2solve/EMB2-2609-V5/Desenvolvimento_IC2S-EBM2-2609-V5.0/Documentos_IC2S-EBM2-2609-V5.0/01-Esquemáticos_IC2S-EBM2-2609-V5.0/png/IC2S_Extension_Board-EBM2_V5-4 Barreira digital.png

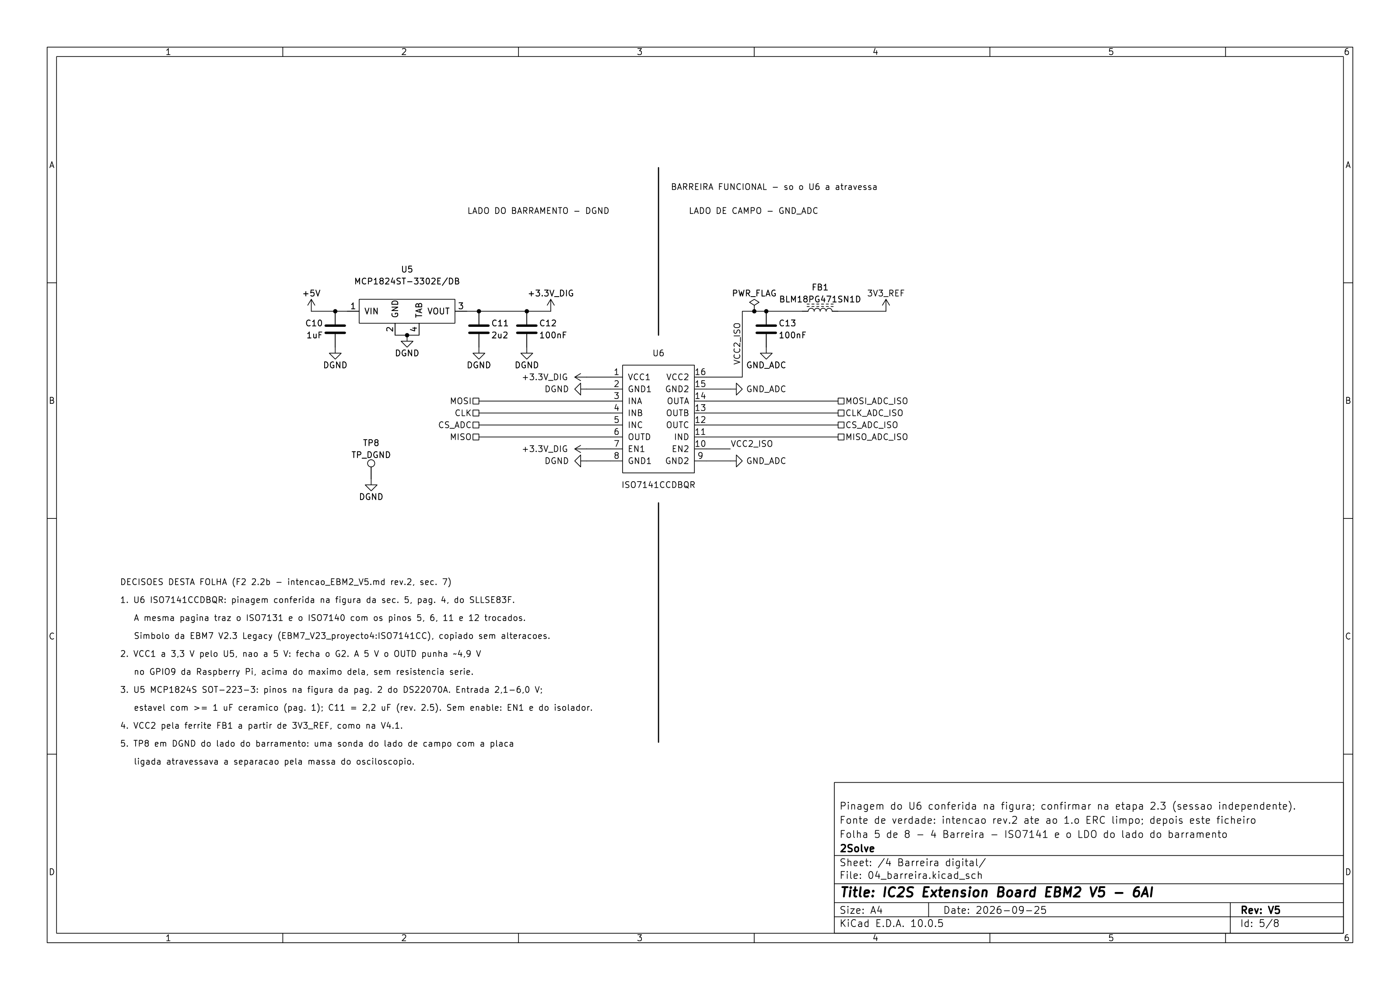
Desenvolvimento_IC2S-EBM2-2609-V5.0/Documentos_IC2S-EBM2-2609-V5.0/01-Esquemáticos_IC2S-EBM2-2609-V5.0/png/IC2S_Extension_Board-EBM2_V5-4 Barreira digital.png
