2solve/EMB2-2609-V5/Desenvolvimento_IC2S-EBM2-2609-V5.0/Documentos_IC2S-EBM2-2609-V5.0/00-Especificações_Técnicas_IC2S-EBM2-2609-V5.0/Verificacoes_F2/verificacao_2_3b_rev25/intencao_EBM2_V5.md

# Documento de intenção — IC2S Extension Board EBM2 V5 (6AI)

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

---

## 1 · O que este documento decide, em poucas linhas

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

## 2 · Estrutura de folhas e designadores

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

### Correspondência V4.1 → V5 das peças herdadas

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

## 3 · Trilhos e domínios

| Rede | Domínio | Origem | Quem a usa |
|---|---|---|---|
| `+24V` | campo, sem isolamento | `P1.20` | folha 02 |
| `GND_24V` | campo | `P1.19` | folha 02, unida a `GND_ADC` por `R200` |
| `+24V_ADC` | campo | `F202` → `D202` | folha 06, laços |
| `+24V_REG` | campo | `F201` → `D201` → `R206` | folha 03 |
| `+5V_ADC` | campo | `TPS7A4001` | folha 03 |
| `+12V_TPS` | campo | `U640` `TPS7A4001` a partir de `+24V_ADC` (**rev. 2.4**) | folha 06, `+Vs` dos `U601`-`U606` |
| `3V3_REF` | campo | `SPX3819`, grampo `TL431` | folhas 03, 04 (`VCC2`), 05, 06 (clamps) |
| `+2V5_REF` | campo | `ADR4525` | folhas 05 (`VREF`) e 07 (topo do divisor) |
| `GND_ADC` | campo | — | todas as de campo |
| `+5V` | **barramento** | `P1.17` | folha 04, entrada do `MCP1824S` |
| `+3.3V_DIG` | **barramento** | `MCP1824S` | folha 04, `VCC1` e `EN1` do isolador |
| `DGND` | **barramento** | `P1.3`, `P1.12`, `P1.16` | folha 04 |

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

## 4 · Folha 01 — conectores

### Ligações, como especificação

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

### Porquê

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

### DFT

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

## 5 · Folha 02 — entrada de 24 V *(desenhada)*

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

**Acrescenta-se nesta folha**, por DFT e por LED (§11):

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

## 6 · Folha 03 — alimentação *(desenhada)*

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

## 7 · Folha 04 — barreira

### Ligações, como especificação

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

`T400`, ponto de prova em `DGND`, **deste lado da barreira**.

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

### Porquê

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

### Dimensionamento

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

### Lógica activa

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

## 8 · Folha 05 — conversor

### Ligações, como especificação

**`U500`, `MCP3208T-BI/SL`**, SOIC-16. Pinagem lida na figura da pág. 1 do
`DS21298E`:

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

### Porquê

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

### Restrições que o firmware tem de cumprir

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

## 9 · Folha 06 — seis laços

### Ligações, como especificação

Por canal *k*, de 1 a 6. Exemplo do canal 1:

`+24V_ADC` → fusível `F601` → `LOOP1_V+`, que vai ao pino 2 de `P2` e alimenta o
transmissor. O retorno chega por `AIN1-`, pino 3 de `P2`. Desse nó sai o TVS
`D601` (cátodo no nó, ânodo a `GND_ADC`) e o **protector de laço `U601` `TPS26613DDFR`**
(**rev. 2.4**, como a EBM7 V2.3 Legacy `U8`-`U11`): pino 4 `IN` no nó `AIN1-`, pino 5 `OUT` em
`AIN1_LIM`, pino 6 `+Vs` em `+12V_TPS` com `C611` 100 nF, pino 7 `VSNS` na rede `VSNS`, pinos
1 `GND`, 2 `MODE` e 3 `−Vs` a `GND_ADC`, pino 8 `SGOOD` sem ligação. ~~`AL5809` e `BAT46W`
antiparalelo~~ saem. De `AIN1_LIM` sai `R601`, **0 Ω 0603** (a posição do `R10` da Legacy). O
outro terminal de `R601` é o nó de medida: burden `R611` 110 Ω a `GND_ADC` e antialias `R621`
3,3 kΩ. O outro terminal de `R621` forma `AIN1_ADC`, com `C601` 100 nF a
`GND_ADC` e o clamp `D621` `BAV199`: pino 3 no sinal, pino 1 a `GND_ADC`, pino 2
a `3V3_REF` (figura da pág. 1 do `BAV199LT1/D`). O TVS `D611` fica entre
~~`+24V_ADC`~~ **`LOOP1_V+`, depois do fusível `F601`, no lado do terminal** (rev. 2.3), e `GND_ADC`.

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

| Peça | Valor | Part number | Pegada | Origem |
|---|---|---|---|---|
| Fusível | 50 mA | `3413.0002.22` | 1206 | Legacy |
| TVS trilho `D611`-`D616` | ~~30 V~~ **36 V** | ~~`824500301`~~ **`824520361`** (SMBJ36A, 600 W) | **DO-214AA** | **rev. 2.2**: a 32 V o trilho chega a 31,4 V, acima dos 30 V de standoff do anterior. É o da EBM7 |
| TVS retorno `D601`-`D606` | ~~36 V~~ **33 V** | **`SMBJ33A-13-F`** (Diodes, a família do `SMBJ36A-13-F` da Legacy) — **datasheet a conferir no pacote da BOM** | DO-214AA | **rev. 2.4**: ver «Porquê» |
| Protector de laço | 25-40 mA, R_ON 4,8-12,5 Ω | ~~`AL5809-25P1-7`~~ **`TPS26613DDFR`** | **SOT-23-8** (md5 igual à Legacy) | **rev. 2.4**, Legacy `U8`-`U11` |
| Desacoplamento `+Vs` | 100 nF 100 V | `GRM188R72A104KA35D` (`C611`-`C616`) | 0603 | Legacy `C26`/`C29`/`C31`/`C32` |
| ~~Schottky antiparalelo~~ | — | ~~`BAT46W-7-F`~~ | — | **sai na rev. 2.4**: o TPS26613 aguenta ±55 V |
| Série | ~~249 Ω~~ ~~150 Ω~~ ~~100 Ω~~ **0 Ω** | `RC0603JR-070RL` | **0603** | **rev. 2.4**: Legacy `R10`; o curto é do `U60x` |
| Burden | 110 Ω 0,1 % 25 ppm | ~~`ERA3AEB111V`~~ **`ERA8AEB111V`** | **1206** | F1 §2.5; **rev. 2.1** |
| Antialias | 3,3 kΩ | `RC0603FR-073K3L` | 0603 | V4.1 |
| Filtro | 100 nF | como V4.1 | 0603 | V4.1 |
| Clamp | — | `BAV199LT1G` | SOT23-3 | Legacy |

`D630` + `R630` 14,7 kΩ: LED de `+24V_ADC` a `GND_ADC`, substitui `D19` (§11).

### Porquê

- **Rev. 2.4 (2026-09-24, decidida pelo projectista): o limitador passa a ser o da EBM7 V2.3
  Legacy, `TPS26613DDFR`** («copiemos como está el EBM7»). A 2.3b reprovou o `AL5809` em três
  linhas (F1 térmica em curto, F2 sempre abaixo dos 2,5 V mínimos, F9 −0,40 V contra −0,3 V).
  Citações do `SLVSFE3C` (TI, rev. C, dez. 2021), na pasta de referências da EBM7:
  - *Curto do transmissor (F1).* `MODE` a `GND`: limita a `I(OL)` 25-40 mA (pág. 5) durante
    `tOL_Expiry` 100 ms, corta, e tenta de novo a cada `tRETRY1` 800 ms (tabela 8-3, pág. 23;
    o `26613` é o de «auto-retry», tabela da pág. 3). No pior caso, a 32 V, com `IN` a
    31,0 V e `OUT` a 40 mA × 110 Ω = 4,4 V, **1,06 W durante 100 ms em cada 900 ms: 0,12 W
    de média, +14 °C** (RθJA 117,8 °C/W, pág. 4). A fig. 7-19 (pág. 12, típica, placa da TI)
    dá, a 85 °C e ~1,05 W, **~200 ms até ao corte térmico** (160 °C): o temporizador de
    100 ms corta antes. Não depende de cobre na F3. **Confirmar no T26.**
  - *Tensão mínima (F2).* Não há: dentro do limite é um interruptor de 4,8-12,5 Ω
    (`RON`, pág. 6). A 20 mA cai **≤ 0,25 V**, contra os 1,6-2,5 V do `AL5809`.
  - *Inversão (F9).* `IN` e `OUT` aguentam ±55 V (pág. 4). Com `−Vs` a `GND`, `OUT` abaixo de
    `−Vs` − 0,2 V corta o FET (`VO_UVLO`, pág. 6, só no 26613/14). **O `BAT46W` sai.**
  - *Alimentação.* Precisa de `+Vs` entre 3 e 30 V (pág. 4) e **acima da tensão de `OUT`**, ou
    corta por `VOUT_OVLO` (`+Vs` + 0,05 V, pág. 5). `OUT` chega a 4,4 V no limite. Copia-se a
    Legacy: **`U640` `TPS7A4001` a 12,09 V** (`R641` 93k1 / `R642` 10k: 1,173 × 10,31) a partir de
    `+24V_ADC`. O `+24V_ADC` não serve: a 32 V fica a 31,4 V, acima dos 30 V recomendados.
    Consumo: 6 × 1,65 mA máx. (pág. 6) + divisores ≈ **10,8 mA**; a 32 V são 0,21 W no `U640`,
    +14 °C (RθJA 66,7 °C/W, SBVS162B pág. 4).
  - *Condensadores do `U640`* (SBVS162B pág. 1 e §8.2.2.2: saída **> 4,7 µF sobre temperatura
    e tolerância**, entrada ≥ 1 µF, recomendados 10 µF). Copiam-se os da Legacy: `C642`
    10 µF 50 V 1206 X5R (`C3216X5R1H106K160AB`, Legacy `C38`; a 12 V a curva da TDK tem de
    dar > 4,7 µF — conferir na BOM) e `C640` 10 µF 100 V 1210 + `C641` 100 nF na entrada
    (Legacy `C35`/`C36`). *A EBM7 V2.3 não Legacy tinha 4,7 µF 25 V 0805: não cumpria.*
  - *`VSNS`* (tabela 8-2, pág. 20). A Legacy tem `R22` 11k5 / `R23`‖`R24` 6k65 → limiar
    descendente 4,46 V. A nota (2) pede-o **acima** de `I_LOOP` × `R_burden`: com `I(OL)` máx.
    40 mA × 110 Ω = 4,40 V, a margem é de 1,4 %, e o `V(SNSF)` de 1 V vem sem mínimo nem
    máximo. **Desvio da Legacy: `R643` 13k3** → limiar descendente **5,0 V** (margem 14 %),
    ascendente 1,72 × 5,0 = **8,6 V** contra `+Vs` mín. 11,8 V; `VSNS` = 2,4 V ≤ 5 V; `R1+R2`
    = 16,6 kΩ ≤ `+Vs`/45 µA = 262 kΩ. `R644`/`R645` 6k65 e `C643` 100 nF, como a Legacy.
  - *`SGOOD` sem ligação*, como na Legacy. **Decisão escrita** (a 2.3b da Legacy pedia-a):
    não há GPIO livre do lado de campo; a falha vê-se na leitura.
  - *`R601` a 0 Ω.* A série de 100 Ω só existia para aguentar o curto sem limitador (V4.1);
    com o limite de 40 mA não protege nada. Fica a ilha, como na Legacy (`R10`). Ganho: +2,0 V
    ao transmissor.
  - *TVS do retorno a 33 V.* `IN` do TPS26613 aguenta **55 V**; o SMBJ36A grampeia a
    **58,1 V** (Würth 824520361, pág. 1). A Legacy usa 30 V (grampo 48,4 V), mas com 30 V de
    standoff os 31,4 V do retorno em curto a 32 V ficam acima (a razão da rev. 2.2). **33 V**:
    standoff 33 V > 31,4 V, grampo 53,3 V a 11,3 A (a classe 33 V do `D200`, Bourns
    SMA6J33A pág. 2) < 55 V. Os `D611`-`D616`, no `LOOPk_V+`, não estão no `IN` e ficam a 36 V.
  - *Comportamento que muda para o firmware.* Em curto a leitura **alterna**: 100 ms a 4095
    (25-40 mA) e 800 ms a ~0 mA (FET desligado → `"null"`). Com a média de 10 amostras em 500
    ms o painel verá sobretudo `"null"`. Avisar o Rodrigo: um `"null"` intermitente com picos a
    4095 é curto, não laço aberto.
  - *Sem `+12V_TPS`* (por exemplo `U640` avariado), o TPS26613 passa ao modo de laço (pág. 20):
    conduz com 5-8,5 V de queda e limita a 22-45,5 mA. A medida continua se o transmissor
    tiver tensão.
- **Topologia copiada da V4.1**, com três valores mudados e já justificados na
  F1: burden 110 Ω, clamp `BAV199`, fusível de 50 mA.
- **Rev. 2.3 (2026-09-23): os seis TVS de laço passam para depois do fusível de canal, no
  terminal `LOOPk_V+`** — como na EBM7 Legacy (`D9`/`D10`/`D12`/`D13` em `+24V_AINk`). Um TVS em
  curto abre só o fusível do seu canal, em vez do `F202` e dos seis canais; um surto do campo
  descarrega no terminal sem atravessar o fusível (resta ~2,9 A de pico entre o grampo de
  58 V e o trilho de 31 V: aguenta 8/20 µs, pode abrir em 10/1000 µs); os surtos da fonte
  ficam só com o `D200` (simplifica a `V7`). Custo: uma fonte externa > 36 V ligada a um
  `LOOPk_V+` leva o TVS desse canal, e só desse. Sem efeito na medida.
- ~~**Os seis TVS de trilho ficam, agora num trilho só.**~~ *(texto da rev. 2, ultrapassado)* Na V4.1 havia dois
  trilhos isolados com três TVS cada. Com um trilho, seis é redundante, mas
  mantém um TVS junto de cada par de pinos de `P2`, que é onde a sobretensão
  entra. A interacção com o `D200` analisa-se na 2.3b (`V7`).
- **O fusível de canal passa a 1206**, porque a peça da Legacy é 1206. O da V4.1
  era 0603. O layout desta zona muda de qualquer forma.
- *[Ultrapassado pela rev. 2.4: fica como histórico da escolha do AL5809.]*
  **Rev. 2.1 (2026-09-23, decidida pelo projectista): limitador por canal, fecha a
  `V8`.** Um transmissor em curto fazia passar 74 mA a 28 V e punha 1,4 W na série
  0603 — defeito herdado da V4.1, cujos `PDM2` não limitavam (curto 1 s, sem
  protecção de sobrecarga). O `AL5809-25` garante 23,75-26,25 mA de −40 a +125 °C
  (DS36625 rev. 5, pág. 4): acima dos 22,7 mA de saturação, logo não se perde
  leitura, e o alarme de 21 mA da NE43 lê-se. **No retorno**, em série com o burden,
  não altera a medida; um curto do `+` à massa não passa por ele e continua a abrir
  o fusível de 50 mA (é essa a razão do fusível, que faltava escrever). O `BAT46W`
  (100 V; V_F máx. 0,25 V a 0,1 mA e 0,45 V a 10 mA, Vishay 86406) protege o −0,3 V
  do `AL5809`; a ~3 mA de falha inversa ficam ~0,40 V, **acima dos −0,3 V: resíduo
  a confirmar na 2.3b**. Série a 150 Ω e burden em 1206 para aguentarem os 26 mA.
  Contas em `ferramentas/avalia_opcoes_V8_RE1.py` e no
  `Relatorio_Melhorias_Isolamento_V8_RE1_2026-09-23.md`. **Pegada do AL5809: Type B,
  duas ilhas iguais — não o PowerDI-123 do KiCad.**

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

### Prova de uma multiplicação

**Rev. 2.4 (TPS26613, `R601` 0 Ω).** A 18 V, 20 mA, `I_tot` = 6 × 20 mA + 10,8 mA (`U640`)
+ 1,5 mA (LED) = 132 mA:

| Parcela | Conta | Queda |
|---|---|---|
| `F202` | 0,8 Ω × 0,132 A | 0,11 V |
| `D202` | V_F máx. a 0,13 A (fig. 2 do MBR1H100SF) | 0,50 V |
| `F60x` | 9,2 Ω × 20 mA | 0,18 V |
| `U60x` | `RON` máx. 12,5 Ω × 20 mA | 0,25 V |
| `R601` + burden | (0 + 110 Ω) × 20 mA | 2,20 V |
| **Sobra ao transmissor** | 18 − 3,24 | **≥ 14,76 V** (era ≥ 10,5 V com o AL5809 e 100 Ω) |

Curto a 32 V: `IN` = 31,4 − 9,2 Ω × 40 mA = 31,0 V; `OUT` = 4,4 V; 26,6 V × 40 mA = 1,06 W
durante 100 ms a cada 900 ms. Burden: 40 mA² × 110 Ω = 0,18 W em pico, 0,02 W de média
(`ERA8AEB111V`, 1206, 0,25 W). Pino do ADC: 4,4 V → pelo `R621` 3,3 kΩ e pelo `BAV199` a
`3V3_REF` ≈ 0,15 mA durante 100 ms (a `V10` continua aberta, por construção).

*Texto das revisões anteriores:*

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

## 10 · Folha 07 — termístor

### Ligações, como especificação

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

### Porquê

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

## 11 · LED indicadores — proposta, a confirmar

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

## 12 · DFT

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

Nove, que é o que `RD1` pede. Três fiduciais na folha 01.

## 13 · Orçamento de erro — resumo

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

## 14 · Verificações abertas

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

## 15 · O que NÃO muda

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

## 17 · Rev. 2.5 — correcções da 2.3b rev. 2.4 (2026-09-24; **2.5b**: R204 4k12 depois de conferir o TL431BQ)

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

| # | Peça | Antes → depois | Porquê (conta e fonte) |
|---|---|---|---|
| 1 | `R206` | 33 Ω → **68 Ω** 0805 anti-surto (MPN: `V5`) | `RA2` do `F201` a 32 V, mesmo método da 2.3b, com os dados do Eaton 4309 pág. 2 (CC12H250mA: resistência a frio típ. 3,5 Ω, I²t de pré-arco típ. 3,8·10⁻⁴ A²s medido a 10 × In, nota 3; confirmado no texto e na imagem da tabela). A curva I²t-tempo da pág. 4 dá ≈ 6·10⁻⁴ a 1,5·10⁻³ A²s a 0,1-0,5 ms, a duração real do arranque: **a margem abaixo é conservadora**. Conta: `V²·C200/(2R)` + `I_LIM²·t` da carga a jusante (`C202` a 5 V, o trilho `3V3_REF` e `C207`). Com os condensadores novos: 47 Ω → **9,4×** (falha), 56 Ω → 10,3×, **68 Ω → 11,2×**. A 18 V, ~7 mA de carga: 0,48 V em `R206`, o `U200` recebe ~17 V (mín. 7 V). Pico 0,45 A, ~1,1 mJ por arranque |
| 2 | `U201` | `SPX3819M5-L-3-3` → **`MCP1824T-3302E/OT`** (SOT-23-5) | O TL431 precisa de > 6 µF no cátodo (fig. 6-18, SLVS543S pág. 18, curva A: fronteira direita ≈ 4,5-6 µF) e o `SPX3819` só especifica electrolítico/tântalo («bench testing is the best method»). O `MCP1824` é estável com cerâmico ≥ 1 µF e recomenda ≤ 22 µF (DS22070A §4.3, pág. 19); VIN 2,1-6,0 V; VOUT 3,3 V ± 2,5 % (pág. 8). Pinagem SOT-23-5 fixa 1 VIN · 2 GND · 3 SHDN · 4 PWRGD · 5 VOUT (tabela 3-1, pág. 17), a mesma geometria do `SPX3819`: muda só o pino 4 |
| 3 | `C208` | 10 nF → **sai** | Era o `BP` do `SPX3819`. No `MCP1824` o pino 4 é `PWRGD` (dreno aberto): fica sem ligação. `EN_3V3` passa a `SHDN_3V3` (`R203` 100 kΩ a `VIN`; limiar máx. 45 % de VIN, §4.6 pág. 20) |
| 4 | `C204` | 2,2 µF → **10 µF 50 V X5R 1206 `C3216X5R1H106K160AB`** | Curva da TDK (ProductDetailed, pág. 2): ≈ 9,4 µF a 3,3 V. Pior caso −10 % −15 % (X5R) → 7,2 µF + 1,3 µF do resto do trilho = **8,5 µF > 6 µF**. Nominal 11,4 µF ≤ 22 µF do `MCP1824` |
| 5 | `R204` | 4k42 → ~~4k22~~ **4k12** (`RC0603FR-074K12L`, **rev. 2.5b**) | TL431**BQ**, tabela 6.13 do SLVS543S (pág. 14): V_ref 2,483-2,507 V a 25 °C; **V_I(dev) 34 mV** (máx.−mín. em −40…125 °C; a 1.ª conta usou 17 mV de memória, errado); I_ref 4 µA + I_I(dev) 2,5 µA; \|z_KA\| 0,5 Ω; ΔV_ref/ΔV_KA −2,7 mV/V. Conservador (os 34 mV inteiros para cada lado, R a 1 %, 46 mA da falha dupla): 4k22 → 3,451-3,688 V (**12 mV** sob 3,70 V); **4k12 → 3,427-3,662 V: 38 mV sob 3,70 V (`RA4`) e 45 mV sobre os 3,3825 V do `MCP1824` (+2,5 %, pág. 8)**, o TL431 não conduz em regime. Os 3,70 V são critério de aceite (`RA4`), não máximo absoluto de peça (MCP3208 7 V, ISO7141 6 V, ADR4525 15 V). I_min real 0,7 mA (não 1 mA) |
| 6 | `C207` | 1,0 µF → **2,2 µF** | Estava no mínimo da tabela 11 do ADR45xx (pág. 35) |
| 7 | `C402` | 1,0 µF → **2,2 µF** | Estava no mínimo do `MCP1824` (§4.3) |
| 8 | `C209`, `C645` | **novos**, 10 nF entre `OUT` e `FB` do `U200` e do `U640` | `C_BYP` (SBVS162B nota 4 pág. 5, §8.2.2.3 pág. 11: «TI highly recommends»). Zero em 1/(2π·32,4 kΩ·10 nF) = 491 Hz (`U200`) e 171 Hz (`U640`) |
| 9 | `C644` | **novo**, 10 µF 50 V `C3216X5R1H106K160AB` em paralelo com `C642` | Curva TDK a 12,6 V ≈ 5,8 µF; com −10 % e −15 % (X5R garantido) uma peça dá 4,4 µF **< 4,7 µF** (SBVS162B pág. 1). Duas: **8,9 µF** |
| 10 | `R661`-`R666` | **novas**, 4k7 0603 (`RC0603FR-074K7L`) entre o nó do filtro (`AINk_FILT`: `C60k`, `D62k`) e o pino do ADC (`AINk_ADC`) | Em curto (`I(OL)` 40 mA × 110 Ω = 4,4 V) o `BAV199` conduz ~0,15 mA e cai **≈ 0,67 V a 25 °C, ≈ 0,72 V a 0 °C** (fig. 2 do BAV199LT1/D): o nó fica acima de `VDD` + 0,6 V por construção (a `V10`). A série limita a corrente para o díodo interno do MCP3208 (modelado com 0,6 V, fig. 4-1 do DS21298E) a **(0,74 − 0,6)/4,7 kΩ ≈ 30 µA**. Custo: fuga típica ≤ 2 nA (fig. 2-39) × 4,7 kΩ ≈ 9 µV; no máximo da tabela (±1 µA) 4,7 mV = 7,7 LSB de offset, que a calibração de campo remove. A carga do C_sample de 20 pF por 4,7 kΩ + 1 kΩ: τ = 114 ns contra 75 µs de amostragem. **Não prova** o limite absoluto de tensão, que o datasheet só dá em tensão: prova-se no T26 e pede-se à Microchip a corrente de injecção |

**Não muda, e porquê:**
- `R601` = 0 Ω. Na falha dupla (`U60x` em curto + 30 V injectados) o burden vê 273 mA / 8,2 W. Voltar a
  100 Ω poria `OUT` a 8,4 V no limite de corrente e o `VSNS` deixava de ter solução entre os 4,4 V e o
  `+12V_TPS` mín. 11,58 V. **Aceite como falha dupla**, documentada.
- `V13` (`+5V_IC` com grampo de 9,2 V contra os 6,5 V do `U401`): medir o barramento num painel.
- O «mínimo de 1 mA» do TL431 (recálculo Sonnet): numa falha simples a corrente injectada (≤ 0,15 mA por
  canal) é menor que a carga de `3V3_REF` (~4 mA); o LDO fornece menos e o TL431 nem conduz. Só a falha
  dupla (46 mA) o põe a regular, bem acima de 1 mA.
- A fig. 7-19 do TPS26613 lida pela 2.3b dá ~140 ms até ao corte térmico a 85 °C (a §9 lia ~200 ms):
  continua acima dos 100 ms do temporizador, com menos margem. Confirmar no T26.

## 16 · Porta de verificação da revisão

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
