2solve/EMB2-2609-V5/Desenvolvimento_IC2S-EBM2-2609-V5.0/Documentos_IC2S-EBM2-2609-V5.0/00-Especificações_Técnicas_IC2S-EBM2-2609-V5.0/Verificacoes_F2/verificacao_2_3b_rev25/planejamento_pcb_EBM2_V5.md

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

# Planejamento do PCB — EBM2 V5

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

---

## 1 · Sumário do produto

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

## 2 · Tabela mestre de componentes

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

> **Designadores definitivos** estão em `intencao_EBM2_V5.md` rev. 2, §2: `U4` passa a `U400`, `U5` a `U500`, o `MCP1824` a `U401`, `R5`/`R8` a `R700`/`R701`. Os desta tabela são os da F1.

### 2.1 · Núcleo de medida

| Ref | Função | Part number | Origem | Justificação |
|---|---|---|---|---|
| `U5` | ADC 12 bits SPI, 8 canais | **`MCP3208T-BI/SL`** | **[HERD]** alterado | **MUDA de `-CI` para `-BI`**: mesmo encapsulamento e pinagem, INL de ±1 LSB em vez de ±2. Ver §2.7b |
| `U4` | Isolador digital 4 canais | `ISO7141CCDBQR` | **[HERD]** | Única barreira da placa. Limiares **TTL**, VIH 2,0 V |
| `U202` | Referência de tensão 2,5 V | `ADR4525BRZ` | **[EBM7]** | ±0,02 % inicial; **4 ppm/°C pelo método bowtie**, que é o que conta a partir de 25 °C. Substitui `VREF` = `VDD` |
| `R×6` | Burden dos laços, 110 Ω | `ERA3AEB111V` (Panasonic) | **[NOVO]** valor | ±0,1 % e ±25 ppm/°C. **É o melhor que existe a 110 Ω — ver §2.5** |
| `R×6` | Série de protecção, 249 Ω | `RC0603FR-07249RL` | **[HERD]** | Não se toca: é protecção. Revisão na 2.3b |
| `R×6` | Anti-aliasing, 3,3 kΩ | `RC0603FR-073K3L` | **[HERD]** | Corte a 482 Hz com 100 nF. **O condensador é o reservatório de carga do ADC — ver §2.7d** |
| `R8` | Divisor do NTC, 5,62 kΩ | `ERA3AEB5621V` | **[HERD]** | Já na V4.1. **Passa a pender de `+2V5_REF` e não de `3V3_REF` — ver §2.7e** |
| `R5` | Termístor de placa, 10 kΩ | `NTCS0603E3103JLT` | **[HERD]** | Canal 4 do ADC. Sensor de temperatura da própria placa |
| `C_VDD` | Desacoplamento do ADC, 1 µF | cerâmico X7R 0603 | **[NOVO]** | **O datasheet pede 1 µF, a V4.1 tem 100 nF.** §6.4, pág. 23 |
| `C_VREF` | Desacoplamento da referência, 1 µF | cerâmico X7R 0603 | **[NOVO]** | Figura 6-3, pág. 23 |
| `D×6` | Clamp de entrada | `BAV199` | **[EBM7]** | Substitui `BAT54S`. Fuga 5 nA a 25 °C contra µA do Schottky |
| `D×12` | TVS de campo, 30 V | `824500301` (Würth) | **[HERD]** | Dois por canal |

### 2.2 · Entrada e protecção de 24 V

| Ref | Função | Part number | Origem | Justificação |
|---|---|---|---|---|
| `D200` | TVS de entrada, 33 V | `SMA6J33A-Q` (Bourns) | **[EBM7]** | A V4.1 **não tem TVS nenhum** na entrada. Grampeia a 58,1 V @ 11,3 A |
| `F202` | Fusível rama dos laços | `CC12H750MA-TR` (Eaton) | **[EBM7]** | I²t de fusão **0,15 A²s**. Margem de arranque **41,7×** — ver §2.6 |
| `F201` | Fusível rama do regulador | `CC12H250MA-TR` (Eaton) | **[EBM7]** família | **MUDOU.** Era «100 mA»; **a série não tem 100 mA**, começa em 250 mA |
| `R206` | Limitador de arranque, 22 Ω 0805 | resistência de impulso, 0805 | **[NOVO]** | **Peça nova, obrigatória.** Sem ela `F201` não cumpre `RA2` — ver §2.6 |
| `D201`, `D202` | Bloqueio, 100 V | `MBR1H100SF` | **[EBM7]** | `D201` serve o regulador e `D202` os laços, como no esquemático. Substitui o zener `D26` em série da V4.1; o `PMEG6010CEH` de 60 V é curto contra 58,1 V |
| `R200` | Net-tie das massas, 0 Ω | `RC0603JR-070RL` | **[EBM7]** | Único caminho `GND_24V` ↔ `GND_ADC` |
| `C200` | Entrada do regulador, 2,2 µF/100 V, **1206** | **MPN por fixar — V6** | **[NOVO]** | Pequeno **de propósito**: é ele que fixa a energia de arranque. **Correcção 2026-09-23:** esta linha dava `GRM31CR72A225KA73L` com origem EBM7. **A EBM7 Legacy não tem nenhum 2,2 µF de 100 V**: os seus 2,2 µF são `C1608X5R1E225K080AB`, 0603 de 25 V, e era daí que vinha a pegada 0603 herdada. O part number não consta do catálogo Murata da pasta. Especificação: 2,2 µF, ≥ 100 V, X7R, 1206, ≥ 1 µF efectivo a 24 V |
| `C201` | Bulk dos laços, 10 µF/100 V | `GRM32EC72A106ME05L` | **[EBM7]** | **Substitui os electrolíticos de 50 V `ESL107M050AGMAA`.** Fecha `G3` |

### 2.3 · Regulação

| Ref | Função | Part number | Origem | Justificação |
|---|---|---|---|---|
| `U200` | Regulador 24 → 4,974 V | `TPS7A4001DGNR` | **[EBM7]** | Entrada 7-100 V, 50 mA máx contra cerca de 12 mA de carga. Divisor 32k4/10k |
| `U201` | LDO 5 → 3,3 V | `SPX3819M5-L-3-3/TR` | **[HERD]** | Já na V4.1 como `U11`. Baixo ruído, último estágio antes do ADC |
| `U203` | Grampo activo a 3,6 V | `TL431BQDBZR` | **[EBM7]** | **Sumidouro dos clamps.** A V4.1 não tem nenhum |
| `U204` | LDO 3,3 V para o isolador | `MCP1824ST-3302E/DB` | **[EBM7]** | **Fecha `G2`.** Datasheet confirmado na pasta |

### 2.4 · Diagnóstico

| Ref | Função | Origem | Justificação |
|---|---|---|---|
| `T20x` | 9 pontos de prova | **[NOVO]** | A V4.1 tem **zero**. Requisito `RD1` |
| `Fid1-3` | 3 fiduciais | **[EBM7]** | A V4.1 tem **zero**. Requisito `RD2` |

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

### 2.5b · O orçamento de erro, com o datasheet do conversor na mão

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

### 2.6 · Os fusíveis, com o datasheet na mão

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

**A série não tem 100 mA.** Começa em 250 mA, e o `F201` de «100 mA» que a
revisão 1 especificava **não é encomendável**.

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

```
I2t = V^2 * C / (2R)        com V = 24 V
```

**Rama dos laços, `F202` = `CC12H750mA`, com `C201` = 10 µF:**

```
I2t = 576 * 10e-6 / (2 * 0,8) = 3,6e-3 A2s
margem = 0,15 / 3,6e-3 = 41,7x           cumpre RA2 (>= 10x)
```

**Rama do regulador, `F201` = `CC12H250mA`, com `C200` = 2,2 µF e mais nada:**

```
I2t = 576 * 2,2e-6 / (2 * 3,5) = 1,81e-4 A2s
margem = 3,8e-4 / 1,81e-4 = 2,1x         REPROVA RA2
```

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

**A solução é a resistência `R206`, e é barata.** Para chegar aos 10× exigidos:

```
I2t <= 3,8e-4 / 10 = 3,8e-5
R   >= 576 * 2,2e-6 / (2 * 3,8e-5) = 16,7 ohm
```

Com o valor normalizado de **22 Ω**, somado aos 3,5 Ω do próprio fusível:

```
I2t = 576 * 2,2e-6 / (2 * 25,5) = 2,48e-5 A2s
margem = 3,8e-4 / 2,48e-5 = 15,3x        cumpre RA2
```

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

```
I2t = 576 * 10e-6 / (2 * 0,51) = 5,65e-3 A2s   ->  3,8x ACIMA do I2t de fusao
I2t = 576 * 10e-6 / (2 * 1,7)  = 1,69e-3 A2s   ->  1,13x ACIMA
```

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

### 2.7 · O conversor: o que o datasheet DS21298E obriga a mudar

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

**Decisão: o mapa de canais fica congelado exactamente como está acima.**

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

#### 2.7b · Porque o grau muda de `-C` para `-B`

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

#### 2.7c · Os erros do conversor são tensões fixas, e é isso que estraga a conta

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

Logo, convertidos a tensão, os limites máximos valem:

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

Orçamento de `RE1` a 25 °C, com o grau `-B` e limites máximos:

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

Cenários avaliados, todos com limites máximos:

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

Orçamento de deriva, `RE2` e `RB3`, para uma excursão de 65 °C:

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

**Cumpre.** Duas notas sobre os números:

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

#### 2.7d · A impedância de fonte: porque 3,3 kΩ é aceitável, e em que condição

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

O que os 3,41 kΩ custam é a **reposição** dessa carga entre amostras:

```
carga por amostra = 20 pF * 2,2 V = 44 pC
queda DC = f_canal * 44 pC * 3410 ohm
```

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

#### 2.7e · O termístor saturava a 70 °C — defeito encontrado e corrigido

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

```
saturacao quando  3,3 * 5,62 / (R_ntc + 5,62) = 2,5   ->  R_ntc = 1,80 kohm
para o NTCS0603E3103 (10 kohm a 25 C, B = 3936 K) isso corresponde a  T = 70 C
```

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

```
V4.1:  codigo = 4096 * (3,3 * ratio) / 3,3 = 4096 * ratio
V5:    codigo = 4096 * (2,5 * ratio) / 2,5 = 4096 * ratio
```

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

#### 2.7f · O resto do que o datasheet obriga

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

## 3 · Interacções entre componentes, em linguagem natural

Este é o texto que a F2 consome.

**Entrada.** Os 24 V entram pelo pino 20 de `P1`, vindos da Universal Baseboard.
Desse nó sai um ponto de prova e o cátodo do TVS `D200`, cujo ânodo vai a
`GND_24V`. Do mesmo nó saem duas ramas em paralelo. A primeira passa pelo
fusível `F202`, entra no ânodo do Schottky `D202`, e o cátodo forma `+24V_ADC`,
que é o rail dos laços: dele saem os seis fusíveis de canal e o bulk `C201`. A
segunda passa por `F201`, entra no ânodo de `D201`, e do cátodo sai a
resistência `R206`, cujo outro terminal forma `+24V_REG`, onde fica `C200` e a
entrada do regulador. **A ordem importa:** `R206` fica depois do díodo e antes
do condensador, porque é entre o fusível e o condensador que ela tem de estar
para limitar o arranque. `GND_24V` liga-se a `GND_ADC` pela resistência de 0 Ω
`R200`, **e por mais nada em toda a placa**.

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

## 4 · Decisões de encapsulamento

| Peça | Encapsulamento | Motivo |
|---|---|---|
| Passivos por omissão | 0603 | O que a V4.1 já usa. Solda manual possível para retrabalho |
| **`R206`** | **0805** | Absorve 0,55 mJ em cada arranque. O 0603 não tem essa margem de impulso |
| Bulk de 100 V | 1210 | A tensão obriga; não há 10 µF/100 V em 0805 |
| Fusíveis | 1206 | Herdado do footprint da V4.1, e é o tamanho da série `CC12H` |
| TVS de entrada | DO-214 (SMA) | Área de dissipação para o pico |
| `TPS7A4001` | HVSSOP-8 com pad térmico | Dissipa cerca de 95 mW; o pad é o caminho |
| `ADR4525` | SOIC-8 | Menos sensível a tensões mecânicas da placa que um SOT pequeno |
| Conectores | THT | **Congelados** por `RC2` |
| Electrolíticos | **eliminados** | Passam a cerâmico 1210. Tira a única peça com vida útil limitada |

Depois desta revisão, as **únicas peças THT são os dois conectores**.

## 5 · Arquitectura de alimentação

```
P1.20 (24 V) --+-- TP -- TVS 33 V --> GND_24V
               |
               +-- F202 750 mA -- D202 --> +24V_ADC --> 6 fusiveis de canal --> campo
               |                              +-- C201 10 uF/100 V + 100 nF
               |                                 (todo o bulk fica deste lado)
               |
               +-- F201 250 mA -- D201 -- R206 22R --> +24V_REG -- C200 2u2/100 V
                                                          |
                                                          +-> TPS7A4001 --> +5V
                                                                 +-> SPX3819 --> 3V3_REF
                                                                       +- ferrite -> VDD do ADC
                                                                       +- ferrite -> VCC2 do isolador
                                                                       +- ADR4525 -> +2V5_REF -+-> VREF do ADC
                                                                       |                       +-> topo do divisor do NTC
                                                                       +- TL431 -> grampo 3,60 V

P1.17 (+5 V) --> MCP1824 --> +3.3V_DIG --> VCC1 e EN1 do isolador        [fecha G2]

GND_24V --[R200 0 ohm]-- GND_ADC           DGND separado pelo ISO7141
```

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

**Empilhamento:** 4 camadas, igual à V4.1.

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

## 6 · Requisitos de DFT incorporados

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

## 7 · Registo de dúvidas

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

### D9 — fechada, e trouxe mais do que se esperava

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

### Calibração: constante comum, e o conflito que isso deixa com `RE1`

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

## 8 · Encerramento do loop

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

| Gap da F0 | Estado |
|---|---|
| G3 electrolíticos | **Fechado**: saem, entram cerâmicos de 100 V |
| G4 fusível da rama do regulador | **Fechado**: `CC12H250mA-TR` mais `R206` de 22 Ω. Margem 15,3× |
| G5 nível de surto inventado | **Fechado**: não há requisito, o critério reescreve-se sem número |
| G6 limite de `3V3_REF` | **Adiado** para a etapa 2.3b, que é onde se derivam os absolutos máximos |
| G7 acesso mecânico | **Fechado**: `RD3` sai do escopo |
| G13 datasheet do `MCP3208` | **Fechado**: fornecido e estudado. Ver §2.7 |

## 8b · O que a F1 deixou por corrigir no esquemático — lista fechada para a F2

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

| # | O que está na folha hoje | O que tem de ficar |
|---|---|---|
| 1 | `F201` com valor `100mA T` | **FEITO 2026-09-23.** `CC12H250MA-TR` |
| 2 | Não existe `R206` | **FEITO 2026-09-23.** 22 Ω em 0805 entre o cátodo de `D201` e a derivação de `C200`. **A versão anterior desta linha dizia `D202`, que é o diodo dos laços: o esquemático provou o contrário e a linha estava errada** |
| 3 | Notas com «1,69 mA2s», «0,37 mA2s», «5,65 mA2s», «1,5 mA2s» | **FEITO 2026-09-23.** Notas refeitas em A²s, e a nota 5, que dizia que `C200` era de 10 µF, corrigida |
| 4 | Ressalva do bloco de título: «F1 formal saltada. MPN do F201 por confirmar» | **FEITO 2026-09-23** |

Um quinto ponto a **verificar**, não a corrigir: a nota 3 da folha estima o
consumo da rama do regulador em cerca de 5 mA e esta F1 usou 12 mA. A conta de
`R206` é insensível à diferença — mesmo a 20 mA a queda seria 0,44 V, contra os
7 V que o `TPS7A4001` precisa e os 19 V disponíveis. Mas o número deve ser
fixado de uma vez na etapa 2.3b, e o `ADR4525` acrescenta-lhe até 950 µA de
corrente de repouso que ainda não estava contada.

### O que o datasheet do conversor acrescentou à lista, para as folhas 05 e 07

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

### Verificações abertas da F2

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

| # | O quê | Porque está aberto | Fecha com |
|---|---|---|---|
| V5 | MPN de `R206`, 22 Ω 0805 anti-surto | Tem de aguentar 0,55 mJ em 56 µs a cada arranque; nenhum datasheet de resistência de impulso está na pasta | Datasheet com curva de impulso |
| V6 | MPN de `C200`, 2,2 µF ≥ 100 V X7R 1206 | O part number candidato não consta do catálogo Murata da pasta | Datasheet com curva de capacidade vs polarização DC |

### Três restrições que não são de hardware e têm de chegar ao firmware

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

## 9 · O erro desta sessão, e o que ele custou

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

Duas tentativas de correcção falharam antes de acertar, e vale registá-las:

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

O que a busca certa mudou no projecto:

| | Revisão 1 | Revisão 2, com o datasheet |
|---|---|---|
| `F201` | «Eaton `CC12H` 100 mA» | `CC12H250mA-TR` — **não existe 100 mA na série** |
| Margem de I²t de `F201` | não calculada | 2,1×, **reprova** `RA2` sem `R206` |
| `R206` | não existia | **peça nova obrigatória**, 22 Ω 0805 |
| Unidades de I²t | «mA²s» | **A²s** — rótulo errado por um factor de 10⁶ |
| Travão do orçamento de erro | «burden de 0,05 % e 10 ppm» | **não existe a 110 Ω** |
| `RE1` | «no limite, 0,182 % contra 0,2 %» | **passa com folga**: eram dois orçamentos, não um |

Cinco dos seis itens são consequência de não ter aberto dois ficheiros.

### Revisão 3, com o datasheet do conversor

O projectista forneceu o `DS21298E` no mesmo dia. O que ele mudou:

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

```yaml
evidencia:
  skill: 2shw-pcb:planejamento
  artefatos: [planejamento_pcb_EBM2_V5.md]
  componentes_total: 27
  componentes_biblioteca: 0
  componentes_novos: 4
  rodadas_entrevista: 1
  duvidas_abertas: 0
  decisoes_de_produto_pendentes: 1
  datasheets_verificados_nesta_fase: 4
  avanco_escopo_pct: 95
```

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
