2solve/EMB2-2609-V5/Desenvolvimento_IC2S-EBM2-2609-V5.0/Documentos_IC2S-EBM2-2609-V5.0/00-Especificações_Técnicas_IC2S-EBM2-2609-V5.0/Verificacoes_F2/verificacao_2_3b_rev24/verificacao_aplicacao_EBM2_V5_rev24.md

# Verificação de aplicação dos datasheets — EBM2 V5 (6AI 4-20 mA) · etapa 2.3b, 2.ª corrida (rev. 2.4)

| | |
|---|---|
| Projecto | IC2S Extension Board EBM2 V5, seis entradas 4-20 mA |
| Etapa | F2 · 2.3b — secção de aplicação de cada CI crítico avaliada com os valores da BOM. **2.ª corrida**, depois da rev. 2.4 da intenção (folha 06: `AL5809` + `BAT46W` → `TPS26613`; trilho `+12V_TPS` com `U640`; `R601` 0 Ω; `D601`-`D606` SMBJ33A) |
| Data | 2026-09-24 |
| Esquemático avaliado | `KiCad_EBM2_V5\` — **só leitura**; netlist `EBM2_V5.net` desta pasta (md5 `ff2181dea6c2`, 131 componentes, 93 redes), `esquematico_EBM2_V5.pdf` (md5 `e26cc040b0e7`) |
| Intenção de referência | `intencao_EBM2_V5.md` rev. 2.4 — **as contas lá escritas foram tratadas como afirmações a conferir**; onde discordo está na §0 e na §4 |
| Envelope | 18–32 V (`RA1`); 0–70 °C de dimensionamento (`RB1`); arranque e dissipação a 32 V, tensão ao transmissor a 18 V |
| Revisor | Sessão nova, **Claude Fable 5.1**, sem o histórico da autoria (autor do esquemático: Claude Opus 5.5). A 1.ª corrida foi assinada pelo mesmo modelo noutra sessão: as linhas da folha 06 foram escritas **antes** de a ler; ver §6 |
| Método | Skill `2shw-pcb:verificar-aplicacao-datasheet`: uma linha por fórmula e por nota; tabela **gerada por avaliação** (`tabela.py` sobre `verificacao_aplicacao_EBM2_V5_rev24_rows.json`); citações por pesquisa no PDF (`grep_datasheet.py`), texto **e** figura renderizada onde o número vem de um gráfico |

> **Veredito da tabela: 174 linhas · 141 cumprem · 16 falham · 17 sem dado.** O `tabela.py` termina com código 1: a etapa **não está fechada**. Das 16 falhas, 11 são as que a 1.ª corrida já tinha e a rev. 2.4 não tocou (duas delas **mudam de natureza** com o TPS26613), 3 são novas ou reclassificadas nesta corrida e 2 são recomendações do fabricante não seguidas (CBYP). **As 6 falhas da 1.ª corrida que dependiam do AL5809/BAT46W deixaram de se aplicar** — o TPS26613 cumpre, com os valores da BOM, todas as linhas da sua secção de aplicação que têm dado para avaliar.

---

## 0 · O que não cumpre, por ordem de consequência

### 0.1 Falhas que pedem decisão antes do Portão 1

| # | Onde | O que o datasheet diz | O que a BOM dá | Consequência | Caminho que proponho (decisão do projectista) |
|---|---|---|---|---|---|
| **N1** | `F201` CC12H250mA, `RA2` (I²t ≥ 10×) a 32 V — **continua da 1.ª corrida (F7), reproduzida de forma independente** | Eaton 4309 p.2: I²t pré-arco típico 0,00038 A²s. SBVS162B p.5: I_LIM do TPS7A4001 51–200 mA; **não há arranque suave no PDF** (a única ocorrência de «soft» é «Tools & Software», p.1) | C200 2,2 µF por R206 33 Ω + 3,5 Ω → 3,09·10⁻⁵ A²s; **mais** a carga de C202/C203 (10,1 µF) pelo I_LIM máximo do U200 → 1,0·10⁻⁵; total 4,09·10⁻⁵ → **9,3×**. Com toda a capacidade a jusante do U200 (≈5,7 µF a 3,3 V): **8,5×**. Com I_LIM típico 117 mA: 10,3×. A 24 V: 13,9× | O planeamento §2.6 diz «C200 e mais nada» e dá 15,3× — ignora o que o regulador puxa pelo fusível no arranque. No fio a 32 V | **R206 = 47 Ω** (0805, anti-surge, MPN a fixar — `V5`): 11,8× no pior caso com C202, 10,6× com toda a capacidade; custa 0,41 V a 8,7 mA, irrelevante para os 7 V do TPS7A4001. Confirmar no ensaio dos 100 ciclos de `RA2` **a 32 V** |
| **N2** | Cadeia do ADC com o protector a regular: `R611` → `R621` → `D621` BAV199 → `3V3_REF` → pino do MCP3208 (`V10`) — **continua da 1.ª corrida (F10), mas passa a ocorrer na falha simples** | SLVSFE3C p.5: I(OL) 25–**40 mA** (MODE = GND). BAV199LT1/D p.2: V_F ≤ 0,90 V @ 1 mA. DS21298E p.2: entradas ≤ V_DD + 0,6 V | Transmissor em curto: 40 mA × 110 Ω = **4,40 V** no burden > 3,23 + 0,6 = 3,83 V → o BAV199 **conduz** (0,06–0,15 mA por canal, 100 ms em cada 900 ms) e o pino fica a `3V3_REF` + V_F = **3,9–4,2 V** contra 3,9 V. Com o AL5809 (26,9 mA → 2,96 V) não conduzia; só acontecia na falha dupla | Máximo absoluto do conversor excedido em até 0,3 V, com dezenas de µA pelo díodo interno (fig. 4-1), durante cada janela de 100 ms de um curto. O datasheet não dá corrente de injecção admissível. A leitura é 4095 de qualquer modo; `RA4` continua a cumprir (0,4–0,9 mA no total ≪ carga do trilho) | Não há solução sem custo: Schottky no lugar do BAV199 mete µA de fuga a 70 °C sobre 3,41 kΩ (vários LSB, parte `RE2`); grampear a `+2V5_REF` cumpre o abs. max (2,5 + 0,9 = 3,4 V) e o ADR4525 absorve 10 mA, mas 6 × 0,3 mA na referência valem ≈1 LSB em todos os canais durante a falha e a falha dupla (8 mA/canal) rebenta o sumidouro. **Proponho manter o BAV199, registar a excursão como comportamento de falha e medi-la no T26** (pino do ADC e `3V3_REF` com um canal em curto a 32 V); pedir à Microchip a corrente de injecção admissível |
| **N3** | `U203` TL431B como grampo de `3V3_REF` — **continua (F3)** | SLVS543S §9.4 p.31: «be sure that the capacitance is within the stability criteria shown in Figure 6-16 and 6-18»; fig. 6-18 p.18 (lida na imagem): curva A (V_KA = V_ref) só sai da zona de oscilação acima de ≈25–45 mA a 3,6 µF | C_L = 3,6 µF cerâmicos (inalterado). Na falha **simples** o grampo já não é solicitado (0,4–0,9 mA < I_min 0,7 mA); na falha dupla (protector em curto, 30 V) entram **46 mA** (6 × 7,7 mA) | Oscilação possível do trilho `3V3_REF` (e de `VDD` do ADC e `VCC2` do isolador) enquanto o grampo conduzir na falha dupla | (a) ≥ 10 µF em `3V3_REF` (zona estável à direita) — obriga a confirmar o SPX3819 com 10 µF cerâmico; (b) ensaio de bancada do grampo; a rev. 2.4 baixou a probabilidade de o grampo actuar, não a falha |
| **N4** | `U203` TL431B, nível do grampo (`RA4` ≤ 3,7 V) — **continua (F4)** | SLVS543S §6.13 p.14 (TL431BQ): V_ref 2,483–2,507 V, V_I(dev) 34 mV, I_ref 4 µA, Z_KA 0,5 Ω | R204 4k42 / R205 10k **sem MPN** (1 % assumido); com I_K = 46 mA da falha dupla nova: **3,73 V** máximo | `RA4` falha por 30 mV no pior caso | R204/R205 a 0,1 % **e** recentrar (R204 4k32 → nominal 3,56 V) — só a tolerância já não chega com 46 mA |
| **N5** | `U401` MCP1824S, entrada `+5V` do barramento (`V13`) — **continua (F5)** | DS22070A p.7: máximo absoluto V_IN 6,5 V | Tecto do `+5V_IC` da base board = grampo do TVS D53: 9,2 V (V_BR 6,7 V) | Falha condicionada à existência do transitório; sem medição do barramento | Medir o `+5V_IC` no painel com transitórios de ligação; senão LDO com abs. max ≥ 10 V ou grampo local ≤ 6 V |
| **N6** | `C207` (ADR4525), `C402` (MCP1824) no mínimo; `C202` (TPS7A4001 U200) sem MPN — **continua (F6, F8)** | ADR45xx Rev. G Tabela 11 p.35: C_OUT **mínimo 1,0 µF** (ADR4525); DS22070A §4.3 p.19: **mínimo 1 µF**; SBVS162B §8.2.2.2 p.11: ≥ 4,7 µF | 1,0 µF nominais (−10 % → 0,9–0,99 µF antes da polarização); C202 10 µF/25 V em **0603** | Nominal igual ao mínimo não é margem; um 0603 de 10 µF a 5 V perde tipicamente 40–60 % | C207/C402 → 2,2–4,7 µF; C202 → 10 µF X7R 0805/1206 com MPN e curva |
| **N7** | `C642` (saída do `U640`, novo) — **falta dado, mas é a linha mais fina do trilho novo** | SBVS162B p.1 / pino OUT p.3: «> 4,7 µF … over temperature and tolerance» | `C3216X5R1H106K160AB` 10 µF/50 V X5R 1206 a 12,1 V e 70 °C, **sem datasheet no disco** `[INHERITED]` Legacy C38 | Com −10 % de tolerância, −15 % de X5R e −30…−40 % de polarização a 24 % da tensão nominal fica em 4,6–5,4 µF: pode ficar **abaixo** de 4,7 µF | Obter a curva TDK antes do Portão 1; se ficar abaixo, 10 µF/50 V X7R 1210 (a EBM7 V2.3 não-Legacy tinha 4,7 µF/25 V e não cumpria — a intenção já o diz) |
| **N8** | `R611` na falha dupla (`RA4` com o protector em curto) — **continua (F12) e agrava-se** | SLVSFE3C Table 9-2 p.27 só cobre o protector a funcionar; Panasonic AOA0000C307 p.2: ERA8A 1206 = 0,25 W | Com `R601` = 0 Ω, 30 V injectados caem inteiros no burden: 273 mA, **8,2 W** (era 2,2 W + 2,0 W com 100 Ω). O caminho `AINk−` → IN → OUT → burden **não passa pelo F60x** | Falha dupla (TPS26613 em curto interno + 30 V no retorno): o burden é destruído — é a topologia da fig. 9-1 do SLVSFE3C e da Legacy, e é a filosofia de falha simples | Manter 0 Ω (Legacy, topologia TI); registar que o TPS26613 é a única protecção do burden e que o fusível de canal não cobre o retorno |

### 0.2 Recomendações não seguidas e falhas informativas

| # | Onde | Achado |
|---|---|---|
| R1 | `U640` e `U200` TPS7A4001, C_BYP | SBVS162B §8.2.2.3 p.11: «TI **highly recommends** using a 10-nF bypass capacitor» entre FB e OUT — não é condição de estabilidade. Nenhum dos dois o tem (redes `FB_U640` e `FB_5V` só com o divisor). Nesta corrida as duas linhas contam como **FALHA de recomendação** (a 1.ª corrida dava «cumpre» com nota ao U200: reclassificada para coerência). Custa um 0603 por regulador; melhora transitório de linha ~10× (fig. 15) |
| R2 | Planeamento §5, «o TPS7A4001 tem arranque suave próprio» | **Não consta do SBVS162B.** Entra na conta de N1. Continua (F14) |
| R3 | `U500` MCP3208, fuga analógica | ±1 µA máximo × 3,41 kΩ = 5,6 LSB de offset por unidade, removido pela calibração de 6 pontos; a deriva vale ≈0,005 LSB. Continua (F11) |
| R4 | `V7`, surto 10/1000 µs pela entrada | No grampo do D200 cada D61x partilha ≈1,39 A pelo fusível de 9,2 Ω: em 10/1000 µs os seis fusíveis de canal abrem. Sem requisito de surto (`RA3` reescrito). Continua (F13) |
| R5 | `F202` CC12H750mA, `RA2` | **Cumpre, mas a margem caiu de 23× para 11,7×**: a rev. 2.4 pôs `C640` 10 µF/100 V no `+24V_ADC` (bulk 20,1 µF). A carga de `C642`/`C61x`/`C643` pelo I_LIM do `U640` acrescenta só 2,6·10⁻⁵ A²s. Só a resistência fria do fusível a limitar o pico (40 A de tecto teórico; I_FSM do D202 50 A) — conservador |
| R6 | `U601`-`U606` fig. 7-19 | A intenção §9 lê «~200 ms até ao corte térmico a 85 °C e ~1,05 W»; na figura ampliada (curva 85 °C) a 1,07 W lê-se **≈140 ms**. Continua acima dos 100 ms do temporizador (1,4×), mas é uma curva típica (I_OUT = 60 mA, MODE = 180 kΩ, placa TI). Se o TSD disparar primeiro, o dispositivo também entra em auto-retry (p.15): não há dano, só muda o ciclo. **Confirmar no T26 a 32 V/70 °C** |
| R7 | `F601`-`F606` a 70 °C | Curva de derating Schurter (p.3, lida na imagem) ≈80 % a 70 °C → 40 mA; o I(OL) máximo de 40 mA fica **exactamente** na corrente nominal derated, durante 100 ms em cada 900 ms (I_RMS 13 mA). Não abre (1,0 × In ≥ 4 h), mas não há margem se a peça derivar |

### 0.3 Sem dado (17 linhas) — a primeira lista de perguntas ao projectista

| Falta | Linhas | Porque interessa |
|---|---|---|
| **Datasheet Diodes `SMBJ33A-13-F`** (`D601`-`D606`) | standoff vs 31,6 V; grampo vs 55 V do IN | A classe 33 V nos PDF Bourns/Würth dá V_RWM 33 V, V_C 53,3 V @ 11,3 A (1,7 V abaixo dos 55 V absolutos; **acima dos 50 V recomendados**, só em surto). Não se assina por designação |
| **Curva TDK `C3216X5R1H106K160AB`** (`C642`) | C_OUT > 4,7 µF do U640 | N7 |
| **Curva Murata `GRM32EC72A106ME05L`** (`C640`) | C_IN ≥ 1 µF do U640 | formalidade (teria de perder 90 %), mas não se assina sem a curva |
| MPN de `C200`, `C202`, `R206` | C_IN/C_OUT do U200; energia de impulso de R206 (1,13 mJ, 73 µs a 32 V) | `V5`/`V6` continuam abertas |
| Corrente nominal do jumper `RC0603JR-070RL` (`R601`) | 40 mA contínuos, 255 mA ≤ 5 µs | Yageo não está no disco; posição do R10 da Legacy |
| **Capacidade de entrada dos transmissores de campo** | arranque com MODE = GND | Q disponível = I(OL)_min × t_OL_Expiry = 25 mA × 100 ms = 2,5 mC ≈ **170 µF a 14,7 V**; acima disso o transmissor não arranca (corta e tenta de 800 em 800 ms). TI reserva o TPS26612 / MODE ≠ GND para «power hungry transmitters» (§9.1 p.26). **Pergunta de requisito de produto** |
| Estabilidade do SPX3819 com cerâmico | U201 | o PDF manda para a bancada |
| V_OH do MCP3208 a 3,3 V; níveis do Raspberry Pi | U400 | não especificado / datasheet ausente |
| Layout (F3): TVS junto ao IN; R(GND burden → AGND) < 5 mΩ; planos do U640; 100 nF a ≤ 2 mm do ISO7141 | 4 linhas | são da F3 |
| t_CSH e frame contínuo | firmware | `expander.js` |

---

## 1 · Âmbito: CI críticos e PDF usados

Todos os PDF estão em `datasheets\` (md5 em `LISTA.md`), excepto o Panasonic, lido **só em leitura** da pasta de referências da EBM7. Páginas = as pesquisadas e citadas; † = figura renderizada e lida na imagem.

| Ref. | Peça | Ficheiro | Revisão | Páginas usadas nesta corrida |
|---|---|---|---|---|
| `U601`-`U606` | TPS26613DDFR | `TI_TPS2661x.pdf` | SLVSFE3C, dez-2021 | 1, 3† (fig. 6-1, Table 6-1), 4, 5, 6, 7, 8, 12† (fig. 7-19 ampliada), 13–19, 20† (Table 8-2), 21, 22, 23 (Table 8-3), 24, 26, 27 (Table 9-1/9-2), 31, 34, 35 (Table 10-1), 36 |
| `U640`, `U200` | TPS7A4001DGNR | `TPS7A4001__TI_TPS7A4001.pdf` | SBVS162B, jul-2015 | 1, 3, 4, 5, 10† (eq. 1, fig. 13), 11, 12, 13; pesquisa «soft», «inrush», «start-up» em todo o PDF |
| `D611`-`D616` | 824520361 (SMBJ36A) | `824520361__Wurth_…pdf` | 001.003, 2023-11-24 | 1, 2 |
| `D601`-`D606` | SMBJ33A-13-F | **não está no disco** | — | linhas `falta dado` |
| `D200` | SMA6J33A-Q | `SMA6J33A__Bourns_SMA6J33A-Q.pdf` | Bourns | 1, 2 (tabela da classe 33 V) |
| `D621`-`D626` | BAV199LT1G | `BAV199__BAV199LT1-D.PDF` | Rev. 12, ago-2024 | 1, 2 |
| `D201`, `D202` | MBR1H100SFT3G | `MBR1H100SF__…pdf` | Rev. 3, jan-2025 | 1, 2, 3† (fig. 1, 2) |
| `F201`, `F202` | CC12H250mA / 750mA | `Eaton_fusible_lento.pdf` | Technical Data 4309, jul-2023 | 1, 2, 3 |
| `F601`-`F606` | 3413.0002.22 | `Schurter_USFF1206_3413.pdf` | 21.07.2026 | 1, 3† (derating, tempo-corrente, tabela), 4 |
| `R611`-`R616` | ERA8AEB111V | `AOA0000C307.pdf` (pasta EBM7, só leitura) | Panasonic ERA | 1, 2 (power rating 85 °C, nota *2), 3 |
| `D630` (e D203/D204) | KG EELP41.22-PHRH-35-A8J8-20-R18 | `KG_EELP41.22__KG-EELP41-22.pdf` | v1.4, 2026-08-07 | 4, 5 |
| `U500` | MCP3208T-BI/SL | `MCP3208__21298e.pdf` | DS21298E, 2008 | 2 (abs. max), 17, 18, 22, 23 + linhas herdadas |
| `U203` | TL431BQDBZR | `TL431__TI_TL431.pdf` | SLVS543S, mai-2024 | 6–14, 18† (fig. 6-18), 27, 31 + linhas herdadas |
| `U202` | ADR4525BRZ | `ADR4525__…pdf` | Rev. G | 1, 3–8, 10, 35 (Table 11) + linhas herdadas |
| `U401` | MCP1824ST-3302E/DB | `MCP1824__22070a.pdf` | DS22070A, 2007 | 1, 2, 7, 19 (§4.3/4.4) + linhas herdadas |
| `U201` | SPX3819M5-L-3-3/TR | `SPX3819__1016_SPX3819.pdf` | rev. 2.0.5 | 1, 2, 3, 7, 8 + linhas herdadas |
| `U400` | ISO7141CCDBQR | `ISO7141__TI_ISO7141CC.pdf` | SLLSE83F, jan-2015 | 5, 21, 22, 25 + linhas herdadas |
| `R700` | NTCS0603E3103JLT | `ntcs0603e3t.pdf` | Vishay | linhas herdadas |
| `P1`, `P2` | Harwin M20-782 | `Harwin_M20-782__…plano.pdf` | plano mecânico (1 pág.) | sem dados eléctricos: fora do âmbito |

Fora do âmbito por não estarem no disco: Diodes SMBJ33A, TDK C3216X5R1H106K160AB, Murata GRM32EC72A106ME05L e BLM18PG471SN1D, Yageo RC0603, Panasonic ERJ3, base board V2.3 e Raspberry Pi. Onde um valor deles era preciso, a linha diz-o e o veredito é *falta dado*.

Valores da BOM: extraídos da netlist com `bom_values.py --around` (U601, U640, F202, D601, D611, D621, R611, U200, U203) e `--net` (`+24V_ADC`, `+12V_TPS`, `3V3_REF`). **Confirmado na netlist**: `U60x` pinos 1/2/3 em `GND_ADC`, 4 em `AINk−` (com `D60x` e `P2`), 5 em `AINk_LIM` (só `R60x`), 6 em `+12V_TPS`, 7 na rede `VSNS` **partilhada pelos seis** (`R643`, `R644`, `R645`, `C643`), 8 sem ligação; `U640` pinos 5 (EN) e 8 (IN) em `+24V_ADC`, 9 (pad) em `GND_ADC`, 3/6/7 abertos; `FB_U640` e `FB_5V` só com o divisor (sem C_BYP). Herdados da EBM7 Legacy (`[INHERITED]`): TPS26613 e a sua ligação, `C61x`, `C640`/`C641`/`C642`, `R641`/`R642`, `R644`/`R645`, `C643`, `R601` 0 Ω — cada um re-derivado contra este circuito (`+Vs` 12,09 V, burden 110 Ω, envelope 18–32 V, 70 °C), não aceite por herança. O desvio declarado da Legacy (`R643` 13k3 em vez de 11k5) confirma-se: nota (2) da Table 8-2 com 14 % de margem em vez de 1,4 %.

**Valores derivados usados em várias linhas** (calculados no gerador, não dactilografados): `+12V_TPS` = 1,173 × (1 + 93,1/10) = **12,094 V**, banda 11,58–12,62 V (±2,5 % de exactidão global do SBVS162B + 1 % em R641/R642); `+24V_ADC` = V_IN − 0,8 Ω × 133 mA − V_F(D202): **17,31 V a 18 V** (V_F máx 0,58 V, fig. 2) e **31,59 V a 32 V** (V_F 0,30 V, tecto); I(+Vs) total no `U640` = 6 × 1,75 mA + 0,76 mA (divisor VSNS) + 0,12 mA (divisor FB) = **11,4 mA**; dissipação do TPS26613 em curto a 32 V = (31,59 − 0,37 − 4,40) × 40 mA = **1,07 W** de pico, 0,119 W de média no ciclo 100/900 ms.

---

## 2 · Tabela de verificação (gerada por `tabela.py`)

Comando: `python tabela.py verificacao_aplicacao_EBM2_V5_rev24_rows.json --lang pt`. As 71 primeiras linhas são as novas desta corrida (folha 06 e o que ela arrasta: `F202`, `F201`, cadeia do ADC); as 103 seguintes vêm da 1.ª corrida, re-avaliadas — as marcadas `[ACTUALIZADA]` tiveram valores mudados pela rev. 2.4 (I(OL) 40 mA, `R601` 0 Ω, `U640`), as `[re-avaliada — BOM inalterada]` mantêm os valores porque a BOM desses CI não mudou. Convenções: V, A, F, Ω, °C, W; `V24_max`/`V24_min` = `+24V_ADC` nos extremos; `Vs_min`/`Vs_max` = `+12V_TPS` nos extremos; `duty` = 100 ms/900 ms.

| CI | fonte (§/tabela/nota, pág.) | fórmula | valores usados | resultado | veredito |
|---|---|---|---|---|---|
| TPS7A4001 U640 (+12V_TPS) | SBVS162B eq. (1) p.10 / fig. 13 | `VOUT = VREF x (1 + R1/R2) ; 1,161 <= VOUT <= 90 V (§6.3)` | VREF=1.173, R1=9.31e+04, R2=1e+04 | VREF*(1+R1/R2) = 12.094 | cumpre |
| TPS7A4001 U640 (+12V_TPS) | SBVS162B eq. (1) p.10 + §6.5 nota (1) p.5 | `VOUT/(R1+R2) >= 10 uA (estabilidade sem carga)` | VOUT=12.094, R1=9.31e+04, R2=1e+04 | VOUT/(R1+R2) = 0.0001173 | cumpre |
| TPS7A4001 U640 (+12V_TPS) | SBVS162B §8.2.2 p.11 | `R1 + R2 <= 500 kOhm (máximo da malha de realimentação)` | R1=9.31e+04, R2=1e+04 | R1+R2 = 1.031e+05 | cumpre |
| TPS7A4001 U640 (+12V_TPS) | SBVS162B §6.5 p.5 (accuracy ±2,5 %) + tolerância 1 % de R641/R642 | `+12V_TPS min/max = VREF x (1 + R1(1-t)/R2(1+t)) x (1-acc) … x (1+acc) — intervalo usado nas linhas do TPS26613` | VREF=1.173, R1=9.31e+04, R2=1e+04, t=0.01, acc=0.025 [DERIVADO] 11,58–12,62 V; a exactidão ±2,5 % está especificada para VIN <= 24 V (nota 2, térmica) — ver linha própria | VREF*(1+R1*(1-t)/(R2*(1+t)))*(1-acc) = 11.580 ; VREF*(1+R1*(1+t)/(R2*(1-t)))*(1+acc) = 12.622 | cumpre |
| TPS7A4001 U640 (+12V_TPS) | SBVS162B §6.3 ROC p.4 | `7 V <= VIN <= 100 V (VIN = +24V_ADC nos extremos)` | V24_min=17.313, V24_max=31.593 [DERIVADO] +24V_ADC = VIN − R_F202·I − V_F(D202); piso com V_F máx 0,58 V (fig. 2), tecto com V_F 0,30 V | V24_min = 17.313 ; V24_max = 31.593 | cumpre |
| TPS7A4001 U640 (+12V_TPS) | SBVS162B §6.5 p.5 (condição VIN >= VOUT(NOM) + 2 V) e VDO 290 mV | `VIN_min >= VOUT + 2 V` | V24_min=17.313, VOUT=12.094 | V24_min - VOUT = 5.220 | cumpre |
| TPS7A4001 U640 (+12V_TPS) | SBVS162B §6.5 nota (2) p.5 | `P = (VIN − VOUT) x IOUT + VIN x IGND ; TJ = TA + P x RthJA <= 125 °C (a 32 V, seis TPS em falha)` | V24_max=31.593, VOUT=12.094, IOUT=0.01138, IGND=6.5e-05, TA=70.000, Rth=66.700 a nota (2) limita a 24 V por dissipação a 50 mA; aqui IOUT = 11,4 mA | (V24_max-VOUT)*IOUT + V24_max*IGND = 0.2239 ; TA + ((V24_max-VOUT)*IOUT + V24_max*IGND)*Rth = 84.934 | cumpre |
| TPS7A4001 U640 (+12V_TPS) | SBVS162B §6.3 IOUT <= 50 mA / §6.5 ILIM 51 mA min | `IOUT = 6 x I(+Vs)_falha + I(R643/R644/R645) + I(R641/R642) <= 50 mA` | I_Vs_flt=0.00175, R1s=1.33e+04, R2s=3325, R1=9.31e+04, R2=1e+04, Vs=12.622 | 6*I_Vs_flt + Vs/(R1s+R2s) + Vs/(R1+R2) = 0.01138 | cumpre |
| TPS7A4001 U640 (+12V_TPS) | SBVS162B p.1 / §8.2.2.2 p.11 / pin OUT p.3 | `COUT > 4,7 uF 'over temperature and tolerance' — C642 10 uF/50 V X5R 1206 a 12,1 V e 70 °C` | C_eff_12V_70C=?, C_min=4.7e-06 [INHERITED] Legacy C38 = C3216X5R1H106K160AB; sem datasheet TDK no disco (LISTA.md): a curva de polarização é obrigatória, X5R a 24 % da tensão nominal pode ficar perto de 4,7 uF | missing: C_eff_12V_70C | **falta dado** |
| TPS7A4001 U640 (+12V_TPS) | SBVS162B p.1 / §8.2.2.2 p.11 | `CIN >= 1 uF 'over temperature and tolerance' — C640 10 uF/100 V a 31,6 V` | C_eff_32V=?, C_min=1e-06 [INHERITED] Legacy C35 = GRM32EC72A106ME05L; sem datasheet Murata no disco. Para falhar teria de perder 90 %: formalidade, mas não se assina sem a curva | missing: C_eff_32V | **falta dado** |
| TPS7A4001 U640 (+12V_TPS) | SBVS162B §8.2.2.3 p.11 | `CBYP = 10 nF entre FB e OUT — 'TI highly recommends' (não é condição de estabilidade)` | C_BYP=0 [RECOMENDAÇÃO] rede FB_U640 só tem R641/R642 na netlist; copiado da Legacy sem CBYP | C_BYP = 0 | **FALHA** |
| TPS7A4001 U640 (+12V_TPS) | SBVS162B §9 p.12 | `Entrada e saída desacopladas com 10 uF junto aos pinos, sem outros componentes entre o condensador e o pino` | C_IN=1e-05, C_OUT=1e-05 valores OK (C640/C642); colocação confere-se na F3 | C_IN = 1e-05 ; C_OUT = 1e-05 | cumpre |
| TPS7A4001 U640 (+12V_TPS) | SBVS162B pin EN p.3 / §6.1 abs max EN-IN <= 0,3 V | `EN ligado a IN: VEN <= VIN sempre ; VEN >= VEN_HI 1,5 V` | V_EN_minus_V_IN=0, V24_min=17.313 netlist: pinos 5 (EN) e 8 (IN) na mesma rede +24V_ADC | V24_min = 17.313 | cumpre |
| TPS7A4001 U640 (+12V_TPS) | SBVS162B pin table p.3 | `PowerPAD ligado ao plano de GND ; NC (3, 6, 7) abertos ou a GND` | pad_gnd=1.000, nc_open=1.000 netlist: pino 9 GND_ADC; pinos 3/6/7 unconnected |  | cumpre |
| TPS7A4001 U640 (+12V_TPS) | SBVS162B §6.5 ILIM p.5 + arranque | `t_arranque = C(+12V_TPS) x VOUT / ILIM_min (informativo; sem soft-start no PDF — 'soft' só aparece em 'Tools & Software', p.1)` | C=1.07e-05, VOUT=12.094, ILIM_min=0.051 o planeamento §5 afirma 'arranque suave próprio': não está no SBVS162B | C*VOUT/ILIM_min = 0.002537 | cumpre |
| TPS7A4001 U640 (+12V_TPS) | SBVS162B §10.1 p.13 + fig. 17 | `Planos de GND de entrada e saída unidos só no pino GND; CIN/COUT/CBYP do mesmo lado da placa, sem vias` | cumprido_F3=? layout: F3 | missing: cumprido_F3 | **falta dado** |
| TPS26613 U601-U606 | SLVSFE3C §7.3 ROC p.4 / Table 10-1 p.35 | `3 V <= +Vs <= 30 V (alimentação única, −Vs = GND)` | Vs_min=11.580, Vs_max=12.622 | Vs_min = 11.580 ; Vs_max = 12.622 | cumpre |
| TPS26613 U601-U606 | SLVSFE3C §7.1 abs max p.4 | `+Vs <= 32 V ; −Vs entre −22 e 0,3 V (−Vs = GND_ADC)` | Vs_max=12.622, V_negVs=0 | Vs_max = 12.622 | cumpre |
| TPS26613 U601-U606 | SLVSFE3C §7.5 Vs_DIFF p.6 | `(+Vs) − (−Vs) >= 3 V` | Vs_min=11.580, V_negVs=0 | Vs_min - V_negVs = 11.580 | cumpre |
| TPS26613 U601-U606 | SLVSFE3C §7.5 VOUT_OVLO p.5 / §9.2.2.1 p.27 | `V(OUT)_max = I(OL)_max x R_burden < (+Vs)_min + 0,05 V (senão o FET corta)` | IOL_max=0.04, R_b=110.000, R_ser=0, Vs_min=11.580 | IOL_max*(R_b+R_ser) = 4.400 ; Vs_min + 0.05 = 11.630 | cumpre |
| TPS26613 U601-U606 | SLVSFE3C Table 8-2 nota (1) p.20 | `(R1 + R2) <= (+Vs) / 45 uA — R1 = R643, R2 = R644||R645` | R1=1.33e+04, R2=3325, Vs_min=11.580 | R1+R2 = 1.662e+04 ; Vs_min/45e-6 = 2.573e+05 | cumpre |
| TPS26613 U601-U606 | SLVSFE3C Table 8-2 nota (1) p.20 — interacção: um divisor para seis pinos VSNS | `(R1 + R2) <= (+Vs) / (6 x 45 uA) (a nota é por dispositivo; a rede VSNS é partilhada por U601-U606)` | R1=1.33e+04, R2=3325, Vs_min=11.580, n=6.000 [INTERPRETAÇÃO do verificador] o datasheet não especifica a corrente do pino VSNS | R1+R2 = 1.662e+04 ; Vs_min/(n*45e-6) = 4.289e+04 | cumpre |
| TPS26613 U601-U606 | SLVSFE3C Table 8-2 nota (2) p.20 | `V(SNSF) x (R1 + R2)/R2 > I_LOOP x R_burden, com I_LOOP = I(OL)_max` | V_SNSF=1.000, R1=1.33e+04, R2=3325, IOL_max=0.04, R_b=110.000 desvio da Legacy (R22 11k5 → R643 13k3) confirmado; V(SNSF) só tem valor típico (p.6): margem 14 % | V_SNSF*(R1+R2)/R2 = 5.000 ; IOL_max*R_b = 4.400 | cumpre |
| TPS26613 U601-U606 | SLVSFE3C Table 8-2 linha '±Vs supplies' p.20 | `+Vs >= V(SNSR) x (R1 + R2)/R2 — para ficar em modo ±Vs e não em loop power` | V_SNSR=1.720, R1=1.33e+04, R2=3325, Vs_min=11.580 | V_SNSR*(R1+R2)/R2 = 8.600 ; Vs_min = 11.580 | cumpre |
| TPS26613 U601-U606 | SLVSFE3C §8.3.5.1 p.20 (texto) | `Usar R1/R2 quando I_LOOP x R_burden > 1,8 V (a 20 mA: 2,2 V) → divisor tem de existir` | I_LOOP=0.02, R_b=110.000, divisor_montado=1.000 | I_LOOP*R_b = 2.200 | cumpre |
| TPS26613 U601-U606 | SLVSFE3C §7.3 ROC VSNS 0-5 V / §7.1 abs max 5,5 V p.4 | `V(VSNS) = (+Vs)_max x R2/(R1+R2) <= 5 V` | Vs_max=12.622, R1=1.33e+04, R2=3325 | Vs_max*R2/(R1+R2) = 2.524 | cumpre |
| TPS26613 U601-U606 | SLVSFE3C Table 6-1 p.3 / §8.3.4 p.19 / §8.3.2 | `−Vs = GND e GND = GND da fonte de +Vs (alimentação unipolar, bloqueio de corrente inversa) ; MODE = GND (0 V, ROC 0-3 V)` | pin1_gnd=1.000, pin3_gnd=1.000, V_MODE=0 netlist: pinos 1, 2, 3 em GND_ADC; pino 6 +12V_TPS; pino 7 VSNS; pino 8 NC | V_MODE = 0 | cumpre |
| TPS26613 U601-U606 | SLVSFE3C §7.3 ROC IN/OUT −50..50 V p.4 | `V(IN) em curto do transmissor a 32 V = +24V_ADC_max <= 50 V` | V24_max=31.593 | V24_max = 31.593 | cumpre |
| TPS26613 U601-U606 | SLVSFE3C §7.1 abs max IN ±55 V p.4 — interacção com D601 (SMBJ33A-13-F) | `V_C(D601) a I_PP < 55 V` | V_C_D601=?, abs_max=55.000 sem datasheet Diodes no disco (LISTA.md). Para a classe 33 V os PDF Bourns/Würth dão 53,3 V @ 11,3 A: 1,7 V de margem, e acima dos 50 V de ROC | missing: V_C_D601 | **falta dado** |
| TPS26613 U601-U606 | Interacção D601 ↔ +24V_ADC | `V_RWM(D601) >= +24V_ADC_max (retorno em curto a 32 V)` | V_RWM_D601=?, V24_max=31.593 sem datasheet; a designação SMBJ33A implica 33 V — não se assina por designação | missing: V_RWM_D601 | **falta dado** |
| TPS26613 U601-U606 | SLVSFE3C §8.3.1 p.15 + §7.5 I(OL) p.5 — dissipação em curto a 32 V | `P = (+24V_ADC_max − I(OL)_max x R_F60x − I(OL)_max x R_burden) x I(OL)_max ; média com tOL_Expiry/(tOL_Expiry+tRETRY1) ; TJ <= 125 °C` | V24_max=31.593, IOL_max=0.04, R_F=9.200, R_b=110.000, duty=0.1111, I_Vs=0.00175, Vs=12.622, TA=70.000, Rth=117.800 Table 8-3 p.23: MODE = GND → 100 ms a I(OL), retry 800 ms; RthJA 117,8 °C/W (p.4, placa JEDEC) | (V24_max - IOL_max*R_F - IOL_max*R_b)*IOL_max = 1.073 ; (V24_max - IOL_max*R_F - IOL_max*R_b)*IOL_max*duty = 0.1192 ; TA + ((V24_max - IOL_max*R_F - IOL_max*R_b)*IOL_max*duty + I_Vs*Vs)*Rth = 86.647 | cumpre |
| TPS26613 U601-U606 | SLVSFE3C fig. 7-19 p.12 (curva TA = 85 °C, lida na figura ampliada) | `t_TSD(P_curto) >= tOL_Expiry 100 ms — o temporizador corta antes do corte térmico` | t_TSD_ms=140.000, tOL_Expiry_ms=100.000 figura típica (IOUT = 60 mA, MODE = 180 kΩ, placa TI); a 1,07 W e 85 °C lê-se ≈140 ms, não ≈200 ms como na intenção §9; usa-se 85 °C porque a média do ciclo põe a junção ≈ +16 °C acima dos 70 °C. Se o TSD disparar primeiro, o dispositivo também faz auto-retry (p.15) | t_TSD_ms/tOL_Expiry_ms = 1.400 | cumpre |
| TPS26613 U601-U606 | SLVSFE3C §7.5 I(FASTRIP) p.5 / §8.3.1 p.15 — interacção com R621/C601 e o pino do MCP3208 | `Corrente prospectiva de curto = +24V_ADC_max/(R_F60x + RON_min + R_burden) ; se > I(FASTRIP) o FET corta em <= 5 us ; degrau no pino do ADC ≈ I x R_b x 5 us/(R621 x C601) <= VDD + 0,6 − 2,5` | V24_max=31.593, R_F=9.200, RON_min=4.800, R_b=110.000, R_aa=3300, C_aa=1e-07, t_ft=5e-06, headroom=1.400 | V24_max/(R_F+RON_min+R_b) = 0.2548 ; (V24_max/(R_F+RON_min+R_b))*R_b*t_ft/(R_aa*C_aa) = 0.4246 | cumpre |
| TPS26613 U601-U606 | SLVSFE3C §7.5 I(OL) min p.5 — interacção com a escala do ADC e NE43 | `I(OL)_min 25 mA >= 22,7 mA (saturação do MCP3208 com VREF 2,5 V e 110 Ω) >= 21 mA (NE43)` | IOL_min=0.025, I_sat=0.02273, I_NE43=0.021 | I_sat = 0.02273 | cumpre |
| TPS26613 U601-U606 | SLVSFE3C §7.5 IQ p.5 | `Erro de medida por fuga IN/OUT: IQ_max x R_burden <= 1/2 LSB (condição V(IN),V(OUT) < +Vs − 0,35 V)` | IQ=1e-07, R_b=110.000, LSB=0.0006104, V_node_max=2.784, Vs_min=11.580 | IQ*R_b = 1.1e-05 ; LSB/2 = 0.0003052 ; V_node_max = 2.784 | cumpre |
| TPS26613 U601-U606 | SLVSFE3C §7.5 RON p.6 | `Queda no protector a 22,7 mA = RON_max x I (só afecta a tensão ao transmissor, não a medida)` | RON_max=12.500, I=0.02273 | RON_max*I = 0.2841 | cumpre |
| TPS26613 U601-U606 | SLVSFE3C §7.5 VO_UVLO p.6 / §8.3.3.3 p.19 / Table 8-1 p.17 — inversão | `OUT < (−Vs) − 0,2..−0,4 V corta o FET; o pino do ADC fica >= −0,4 V >= −0,6 V (abs max MCP3208 p.2). O 26613 NÃO tem UVLO de IN (Table 8-1)` | V_OUT_min=-0.4, abs_min_ADC=-0.6 com IN negativo conduz primeiro o D601 em directo: caminho limitado só pela fonte de campo — ver «o que nenhuma ferramenta viu» | V_OUT_min = -0.4 | cumpre |
| TPS26613 U601-U606 | SLVSFE3C §11.1 p.36 | `Pelo menos 100 nF junto a +Vs de cada dispositivo — C611..C616 100 nF/100 V` | C_Vs=1e-07 | C_Vs = 1e-07 | cumpre |
| TPS26613 U601-U606 | SLVSFE3C §11.1 p.36 | `TVS junto ao pino IN (D601 em AINk−) ; percurso de corrente do laço curto` | d_TVS_IN_mm=? layout: F3 | missing: d_TVS_IN_mm | **falta dado** |
| TPS26613 U601-U606 | SLVSFE3C §11.1 p.36 + planeamento §5 | `Ambos os terminais do burden encaminhados diferencialmente ao ADC — aqui o MCP3208 é single-ended: exige R(GND burden → AGND) < 5 mΩ (queda < 1 LSB a 120 mA)` | R_gnd_mohm=? layout: F3 (restrição do planeamento §5) | missing: R_gnd_mohm | **falta dado** |
| TPS26613 U601-U606 | SLVSFE3C Table 8-3 p.23 / §9.1 p.26 — arranque de transmissor a 2 fios com MODE = GND | `Carga que o transmissor pode absorver no arranque sem disparar o corte: I(OL)_min x tOL_Expiry >= C_tx x V_loop (TI reserva o 26612/MODE≠GND para 'power hungry transmitters')` | IOL_min=0.025, tOL=0.1, C_tx=?, V_loop=14.700 capacidade de entrada dos transmissores de campo desconhecida: pergunta ao projectista/campo. Q disponível = 2,5 mC ≈ 170 uF a 14,7 V | missing: C_tx | **falta dado** |
| TPS26613 U601-U606 | SLVSFE3C §8.3.5 p.20 (loop power mode sem +Vs) | `Sem +12V_TPS o dispositivo conduz com queda 5–8,5 V e limita a 22–45,5 mA: a medida continua (informativo) e o nó do burden sobe a 45,5 mA x 110 Ω` | IOL_noVs_max=0.0455, R_b=110.000, Vs_min_plus=11.630 | IOL_noVs_max*R_b = 5.005 | cumpre |
| R611-R616 ERA8AEB111V (burden) | SLVSFE3C Table 9-2 p.27 (MODE = GND, 40 mA) + Panasonic AOA0000C307 p.2 (ERA8A 1206: 0,25 W a 85 °C) | `P_pico = I(OL)_max^2 x R_burden <= 0,25 W (a 70 °C não há derating: começa a 85 °C)` | IOL_max=0.04, R_b=110.000, P_rated=0.25 | IOL_max**2*R_b = 0.176 | cumpre |
| R611-R616 ERA8AEB111V (burden) | idem — média no ciclo 100 ms/900 ms | `P_média = P_pico x duty <= 0,25 W` | IOL_max=0.04, R_b=110.000, duty=0.1111, P_rated=0.25 | IOL_max**2*R_b*duty = 0.01956 | cumpre |
| R611-R616 ERA8AEB111V (burden) | Panasonic AOA0000C307 p.2 nota *2 (RCWV = sqrt(P x R)) | `V_burden em curto = I(OL)_max x R_b <= RCWV` | IOL_max=0.04, R_b=110.000, P_rated=0.25 | IOL_max*R_b = 4.400 ; sqrt(P_rated*R_b) = 5.244 | cumpre |
| R611-R616 ERA8AEB111V (burden) | Teste de uma multiplicação (escopo RM2/planeamento §2.5) | `20 mA x 110 Ω = 2,200 V <= VREF 2,5 V ; 22,7 mA = fundo de escala` | I=0.02, R_b=110.000, VREF=2.500 | I*R_b = 2.200 ; I*R_b/VREF = 0.88 | cumpre |
| R601-R606 RC0603JR-070RL (0 Ω) | Yageo RC0603 jumper — corrente nominal | `I(OL)_max 40 mA (e pico 255 mA <= 5 us) <= I_nominal do jumper` | IOL_max=0.04, I_rated=? sem datasheet Yageo no disco; posição do R10 da Legacy | missing: I_rated | **falta dado** |
| R621/C601 + D621 BAV199 + MCP3208 (cadeia do ADC) | BAV199LT1/D p.2 (VF <= 0,9 V @ 1 mA, majorante) + DS21298E p.2 (abs max VDD + 0,6 V) — V10 | `Transmissor em curto: V_pino = 3V3_REF + VF(BAV199) com I_clamp = (I(OL)_max x R_b − 3V3_REF − VF)/R621 ; V_pino <= VDD + 0,6` | IOL_max=0.04, R_b=110.000, V33=3.300, VF_max=0.9, R_aa=3300, VDD=3.300 majorante: VF a 0,06 mA é < 0,9 V (o PDF só tabela 1/10/50/150 mA); com VF típico ≈0,6 V fica ≈3,9 V — no limite. O díodo interno do MCP3208 grampeia a VDD+0,6 com dezenas de uA: sem dano, mas fora do abs max formal | V33 + VF_max = 4.200 ; VDD + 0.6 = 3.900 ; (IOL_max*R_b - V33 - VF_max)/R_aa = 6.061e-05 | **FALHA** |
| R621/C601 + D621 BAV199 + MCP3208 (cadeia do ADC) | escopo RA4 (3V3_REF <= 3,7 V com 30 V numa entrada) — sumidouro do clamp | `6 canais em curto: I_clamp_total = 6 x (I(OL)_max x R_b − 3,3 − 0,6)/R621 << carga do trilho (TL431 grampeia a 3,60 V só se o trilho subir)` | IOL_max=0.04, R_b=110.000, R_aa=3300, I_load_3V3_min=0.002 carga mínima do 3V3_REF (MCP3208 + ADR4525 + ISO7141 lado 2) tomada por baixo em 2 mA; o TL431 (R204/R205 → 3,60 V) é a rede de segurança | 6*(IOL_max*R_b - 3.3 - 0.6)/R_aa = 0.0009091 | cumpre |
| R621/C601 + D621 BAV199 + MCP3208 (cadeia do ADC) | BAV199LT1/D p.2 (IR 5 nA @ 70 V/25 °C, 80 nA @ 150 °C) | `Erro por fuga do clamp: IR x R621 <= 1/2 LSB` | IR=8e-08, R_aa=3300, LSB=0.0006104 | IR*R_aa = 0.000264 ; LSB/2 = 0.0003052 | cumpre |
| D611-D616 824520361 (SMBJ36A, LOOPk_V+) | Würth 824520361 p.1 | `V_DC (standoff) 36 V >= +24V_ADC_max` | V_RWM=36.000, V24_max=31.593 | V24_max = 31.593 | cumpre |
| D611-D616 824520361 (SMBJ36A, LOOPk_V+) | Würth 824520361 p.1 | `V_BR min = 42,1 V x 0,95 >= +24V_ADC_max` | V_BR=42.100, tol=0.05, V24_max=31.593 | V_BR*(1-tol) = 39.995 | cumpre |
| D611-D616 824520361 (SMBJ36A, LOOPk_V+) | Würth p.1 V_clamp 58,1 V @ 10,4 A — escopo RA3 aplicado ao trilho de laço | `V_C <= menor abs max a jusante de LOOPk_V+: F60x 63 VDC (Schurter p.1), C201/C640 100 V, D202 100 V (MBR1H100SF p.2), U640 105 V (SBVS162B p.4)` | V_C=58.100, abs_min=63.000 | V_C = 58.100 ; abs_min = 63.000 | cumpre |
| D611-D616 824520361 (SMBJ36A, LOOPk_V+) | Würth p.1 (I_Leak 1 uA @ 36 V) — interacção com a medida | `Fuga do D61x flui de LOOPk_V+ para GND antes do transmissor: não passa no burden → erro de medida = 0 x R_b` | I_leak=1e-06, no_burden=0 | I_leak*no_burden*110 = 0 | cumpre |
| F601-F606 3413.0002.22 (50 mA) | Schurter USFF1206 p.3 curva de derating (lida na figura: ≈80 % a 70 °C) | `I_normal <= In x derating(70 °C) ; 22,7 mA vs 50 mA x 0,8` | I_max_normal=0.02273, In=0.05, derate=0.8 | I_max_normal/(In*derate) = 0.5682 | cumpre |
| F601-F606 3413.0002.22 (50 mA) | Schurter p.3 pre-arcing 1,0 x In >= 4 h — falha com TPS26613 | `I(OL)_max 40 mA <= In x derating (o curto do transmissor não abre o fusível de canal: é o protector que actua) ; I_RMS do ciclo = 40 mA x sqrt(duty)` | IOL_max=0.04, In=0.05, derate=0.8, duty=0.1111 | IOL_max/(In*derate) = 1 ; IOL_max*sqrt(duty) = 0.01333 | cumpre |
| F601-F606 3413.0002.22 (50 mA) | Schurter p.3 I2t 0,0002 A2s (8 In) + breaking 100 A @ 63 VDC | `Curto de LOOPk_V+ a GND: I = +24V_ADC_max/R_fus ; t_fusão = I2t/I^2 ; I <= 100 A` | V24_max=31.593, R_F=9.200, I2t=0.0002, I_break=100.000 | V24_max/R_F = 3.434 ; I2t/(V24_max/R_F)**2 = 1.696e-05 | cumpre |
| F601-F606 3413.0002.22 (50 mA) | Schurter p.1 tensão nominal 63 VDC | `V_C(D61x) 58,1 V <= 63 V` | V_C=58.100, V_rated=63.000 | V_C = 58.100 | cumpre |
| F601-F606 3413.0002.22 (50 mA) | Schurter I2t 0,0002 A2s — surto 8/20 us descarregado no D61x (intenção §9, rev. 2.3) | `I_retorno = (V_C − +24V_ADC_max)/R_fus ; I^2 x 20 us <= I2t (informativo: não há requisito de imunidade, RA3)` | V_C=58.100, V24_max=31.593, R_F=9.200, I2t=0.0002, t=2e-05 margem 1,2x com o valor típico do I2t; em 10/1000 us abre (a intenção já o diz) | (V_C-V24_max)/R_F = 2.881 ; ((V_C-V24_max)/R_F)**2*t = 0.000166 ; I2t = 0.0002 | cumpre |
| F202 CC12H750mA + D202 (RA2) | Eaton 4309 p.2 + planeamento §2.6 ; escopo RA2 (>= 10x) — a 32 V com C201 + C640 + C641 | `I2t = V^2 C/(2 R_fus) ; margem = I2t_fusão/I2t >= 10` | V=32.000, C=2.01e-05, R=0.8, I2t_f=0.15 a rev. 2.4 duplicou o bulk (C640): a margem cai de 41,7x (24 V, 10 uF, planeamento) para 11,7x; só a resistência do fusível a limitar (conservador) | V**2*C/(2*R) = 0.01286 ; I2t_f/(V**2*C/(2*R)) = 11.660 | cumpre |
| F202 CC12H750mA + D202 (RA2) | idem + SBVS162B ILIM 200 mA max — carga de C642/C61x/C643 pelo U640 | `I2t_total = I2t(C24V) + ILIM_max^2 x (C12V x VOUT/ILIM_max) ; margem >= 10` | V=32.000, C=2.01e-05, R=0.8, I2t_f=0.15, ILIM=0.2, C12=1.07e-05, VOUT=12.094 | ILIM**2*(C12*VOUT/ILIM) = 2.588e-05 ; I2t_f/(V**2*C/(2*R) + ILIM**2*(C12*VOUT/ILIM)) = 11.637 | cumpre |
| F202 CC12H750mA + D202 (RA2) | Eaton 4309 p.2 nota 3 (I2t medido a 10 In) — pico de arranque | `I_pico = V/R_fus (limite superior) ; I_pico <= I_FSM(D202) 50 A (MBR1H100SF p.2, 8,3 ms) ; o I2t a 53 In pode ser menor que o típico a 10 In` | V=32.000, R=0.8, IFSM=50.000 tau = R x C = 16 us; o pico real é menor (V_F do D202, ESR, cablagem) | V/R = 40.000 | cumpre |
| F202 CC12H750mA + D202 (RA2) | Eaton 4309 p.2 (100 % 4 h min) | `I_regime = 6 x 20 mA + U640 + LED <= 750 mA ; falha 6 x 40 mA` | I_reg=0.1335, I_flt=0.2535, In=0.75 | I_reg = 0.1335 ; I_flt = 0.2535 | cumpre |
| F202 CC12H750mA + D202 (RA2) | Eaton 4309 p.2 (63 VDC) + Bourns SMA6J33A p.2 (V_C 53,3 V) — RA3 | `V_C(D200) <= 63 V` | V_C=53.300, V_rated=63.000 | V_C = 53.300 | cumpre |
| F201 CC12H250mA + R206 + U200 (RA2) | Eaton 4309 p.2 + planeamento §2.6 — a 32 V, só C200 (a conta do planeamento, a 24 V, dava 15,3x com 22 Ω) | `I2t = V^2 C200/(2 (R_fus + R206)) ; margem >= 10` | V=32.000, C=2.2e-06, R_f=3.500, R206=33.000, I2t_f=0.00038 | V**2*C/(2*(R_f+R206)) = 3.086e-05 ; I2t_f/(V**2*C/(2*(R_f+R206))) = 12.314 | cumpre |
| F201 CC12H250mA + R206 + U200 (RA2) | idem + SBVS162B §6.5 ILIM p.5 (51–200 mA; sem soft-start no PDF) — carga de C202/C203 pelo U200 | `I2t_total = I2t(C200) + ILIM^2 x (C5V x VOUT/ILIM), ILIM = 200 mA máx ; margem >= 10` | V=32.000, C=2.2e-06, R_f=3.500, R206=33.000, I2t_f=0.00038, ILIM=0.2, C5=1.01e-05, VOUT=4.974 o planeamento §2.6 diz 'C200 e mais nada': ignora os 10 uF de C202 atrás do LDO; o LDO limita a corrente mas não a energia que o fusível vê | ILIM**2*(C5*VOUT/ILIM) = 1.005e-05 ; V**2*C/(2*(R_f+R206)) + ILIM**2*(C5*VOUT/ILIM) = 4.091e-05 ; I2t_f/(V**2*C/(2*(R_f+R206)) + ILIM**2*(C5*VOUT/ILIM)) = 9.289 | **FALHA** |
| F201 CC12H250mA + R206 + U200 (RA2) | idem com ILIM típico 117 mA | `mesma conta com ILIM típico` | V=32.000, C=2.2e-06, R_f=3.500, R206=33.000, I2t_f=0.00038, ILIM=0.117, C5=1.01e-05, VOUT=4.974 | I2t_f/(V**2*C/(2*(R_f+R206)) + ILIM**2*(C5*VOUT/ILIM)) = 10.344 | cumpre |
| F201 CC12H250mA + R206 + U200 (RA2) | idem, com toda a capacidade a jusante do U200 (C204..C208, C207, C501/502, C403, C500, C601-606, C700 ≈ 5,7 uF a 3,3 V) e ILIM máx | `I2t_total = I2t(C200) + ILIM^2 x [(C5V x 4,97 + C3V3 x 3,3)/ILIM] ; margem >= 10` | V=32.000, C=2.2e-06, R_f=3.500, R206=33.000, I2t_f=0.00038, ILIM=0.2, C5=1.01e-05, VOUT=4.974, C33=5.4e-06 | I2t_f/(V**2*C/(2*(R_f+R206)) + ILIM*(C5*VOUT + C33*3.3)) = 8.545 | **FALHA** |
| F201 CC12H250mA + R206 + U200 (RA2) | MBR1H100SF p.2 I_FSM 50 A | `I_pico(F201) = V/(R_fus + R206) <= I_FSM(D201)` | V=32.000, R_f=3.500, R206=33.000, IFSM=50.000 | V/(R_f+R206) = 0.8767 | cumpre |
| F201 CC12H250mA + R206 + U200 (RA2) | intenção V5 — energia de impulso em R206 | `E = 1/2 C200 V^2 em tau = (R_fus+R206) C200 <= energia de impulso admissível do MPN` | C=2.2e-06, V=32.000, E_pulse_rated=? R206 sem MPN na netlist (V5 aberta) | missing: E_pulse_rated | **falta dado** |
| D630 KG EELP41.22 + R630 14k7 | KG EELP41.22 p.4 (IF 0,5–30 mA) e p.5 (VF 1,6–2,4 V) | `0,5 mA <= (V24 − VF)/R630 <= 30 mA nos dois extremos` | V24_max=31.593, V24_min=17.313, VF_min=1.600, VF_max=2.400, R=1.47e+04 | (V24_max-VF_min)/R = 0.00204 ; (V24_min-VF_max)/R = 0.001015 | cumpre |
| U200 TPS7A4001 | SBVS162B §6.3 Rec. Op., p.4 | `VIN >= 7 V (mín. recomendado)` | VIN_MIN=18.000, R_F201=3.500, VF_D201=0.45, R206=33.000, I_REG=0.008734 [1.ª corrida, re-avaliada — BOM inalterada na rev. 2.4] entrada a 18 V (RA1) | VIN_MIN - R_F201*I_REG - VF_D201 - R206*I_REG = 17.231 | cumpre |
| U200 TPS7A4001 | SBVS162B §6.1 Abs. max, p.4 | `IN, EN <= 105 V (abs.) ; §6.3 VIN <= 100 V` | VC_D200=53.300 [1.ª corrida, re-avaliada — BOM inalterada na rev. 2.4] no grampo do D200 (Bourns p.2, I_PP 11,3 A) | VC_D200 = 53.300 | cumpre |
| U200 TPS7A4001 | SBVS162B §8.1.1 Eq.1 / Fig.13, p.10 | `VOUT = VREF x (1 + R1/R2)  [R1=R201 OUT→FB, R2=R202 FB→GND]` | VREF=1.173, R1=3.24e+04, R2=1e+04 [1.ª corrida, re-avaliada — BOM inalterada na rev. 2.4] | VREF*(1+R1/R2) = 4.974 | cumpre |
| U200 TPS7A4001 | SBVS162B §6.5 nota(1) p.5 + §8.1.1 p.10 | `VOUT/(R1+R2) >= 10 µA (estabilidade sem carga)` | VOUT=4.974, R1=3.24e+04, R2=1e+04 [1.ª corrida, re-avaliada — BOM inalterada na rev. 2.4] | VOUT/(R1+R2) = 0.0001173 | cumpre |
| U200 TPS7A4001 | SBVS162B §8.2.2, p.11 | `R1 + R2 <= 500 kΩ (máx. de realimentação)` | R1=3.24e+04, R2=1e+04 [1.ª corrida, re-avaliada — BOM inalterada na rev. 2.4] | R1+R2 = 4.24e+04 | cumpre |
| U200 TPS7A4001 | SBVS162B §6.5 p.5 (VREF 1,161–1,185) + R ±1 % | `banda de +5V_ADC = VREF_min/max x (1 + R1/R2) com R1/R2 ±2 %` | VREF_MIN=1.161, VREF_MAX=1.185, ratio=3.240 [1.ª corrida, re-avaliada — BOM inalterada na rev. 2.4] limites: VIN mín do SPX3819 = 3,3+0,25 V ; VIN máx SPX3819 16 V | VREF_MIN*(1+ratio*0.98) = 4.847 ; VREF_MAX*(1+ratio*1.02) = 5.101 | cumpre |
| U200 TPS7A4001 | SBVS162B §6.1 Abs. max, p.4 | `FB pin <= 2 V` | V_FB=1.185 [1.ª corrida, re-avaliada — BOM inalterada na rev. 2.4] | V_FB = 1.185 | cumpre |
| U200 TPS7A4001 | SBVS162B §8.2.2.2, p.11 | `COUT >= 4,7 µF (mín. p/ estabilidade; 10 µF recomendado) — capacidade EFECTIVA a 5 V` | C202_nominal=1e-05, C202_efectiva_5V=? [1.ª corrida, re-avaliada — BOM inalterada na rev. 2.4] C202 = 10 µF/25 V em 0603 (X5R): perda por polarização DC a 5 V tipicamente 40–60 %; sem MPN não se prova ≥ 4,7 µF | missing: C202_efectiva_5V | **falta dado** |
| U200 TPS7A4001 | SBVS162B §8.2.2.2, p.11 (+ §9 p.12: 10 µF junto ao pino) | `CIN >= 1 µF — capacidade EFECTIVA a 32 V` | C200_nominal=2.2e-06, C200_efectiva_32V=? [1.ª corrida, re-avaliada — BOM inalterada na rev. 2.4] V6 aberta: sem MPN de C200 não há curva de polarização; §9 recomenda 10 µF | missing: C200_efectiva_32V | **falta dado** |
| U200 TPS7A4001 | SBVS162B §8.2.2.3, p.11 | `CBYP = 10 nF entre FB e OUT («highly recommended», não exigido p/ estabilidade)` | CBYP_nF=0 [1.ª corrida, ACTUALIZADA para a rev. 2.4] [RECOMENDAÇÃO, não requisito de estabilidade] tratamento igual ao do U640 nesta corrida (a 1.ª dava 'cumpre' com nota) | CBYP_nF = 0 | **FALHA** |
| U200 TPS7A4001 | SBVS162B §10.4 Eq.2 + §6.4 RθJA 66,7 °C/W, p.4/14 | `PD = (VIN−VOUT)·IOUT + VIN·IGND ; TJ = 70 + PD·RθJA <= 125 °C` | V_REG=31.231, VOUT=4.974, I_REG=0.008734, I_GND=6.5e-05, RthJA=66.700, TA=70.000 [1.ª corrida, re-avaliada — BOM inalterada na rev. 2.4] a 32 V; I_REG soma ICC2 ISO7141 4,9 + MCP3208 0,4 + ADR4525 1,42 + SPX 0,25 + LED 1,58 + divisor 0,12 mA | (V_REG-VOUT)*I_REG + V_REG*I_GND = 0.2314 ; TA + ((V_REG-VOUT)*I_REG + V_REG*I_GND)*RthJA = 85.432 | cumpre |
| U200 TPS7A4001 | SBVS162B §6.5 nota(2), p.5 | `«VIN limitado a 24 V pela dissipação a plena carga (50 mA)» → PD(32 V, carga real) <= (24−VREF)·50 mA = 1,14 W` | V_REG=31.231, VOUT=4.974, I_REG=0.008734 [1.ª corrida, re-avaliada — BOM inalterada na rev. 2.4] a nota permite >24 V se a dissipação couber | (V_REG-VOUT)*I_REG = 0.2293 | cumpre |
| U200 TPS7A4001 | SBVS162B §10.3, p.14 | `protecção térmica (170 °C) deve disparar >= 45 °C acima da ambiente máxima` | TSD=170.000, PD=0.2293, RthJA=66.700, TA=70.000 [1.ª corrida, re-avaliada — BOM inalterada na rev. 2.4] | TSD - PD*RthJA = 154.703 | cumpre |
| U200 TPS7A4001 | SBVS162B §6.3, p.4 | `IOUT <= 50 mA` | I_REG=0.008734 [1.ª corrida, re-avaliada — BOM inalterada na rev. 2.4] | I_REG = 0.008734 | cumpre |
| U200 TPS7A4001 | SBVS162B §6.5 p.5 | `VEN_HI >= 1,5 V (EN ligado a IN)` | V_REG_18=17.231 [1.ª corrida, re-avaliada — BOM inalterada na rev. 2.4] | V_REG_18 = 17.231 | cumpre |
| U200 TPS7A4001 | SBVS162B — pesquisa «soft»: 0 ocorrências | `arranque suave («arranque suave próprio», planejamento §5) — existe no datasheet?` | ocorrencias_soft=0 [1.ª corrida, re-avaliada — BOM inalterada na rev. 2.4] não consta: o arranque só é limitado por ILIM 51–200 mA (p.5) | ocorrencias_soft = 0 | **FALHA** |
| U201 SPX3819 | SPX3819 Operating Ratings, p.2 | `2,5 V <= VIN <= 16 V (V2 da intenção)` | V5_MIN=4.847, V5_MAX=5.101 [1.ª corrida, re-avaliada — BOM inalterada na rev. 2.4] | V5_MIN = 4.847 ; V5_MAX = 5.101 | cumpre |
| U201 SPX3819 | SPX3819 Abs. Max, p.2 | `VIN, EN dentro de −20..+20 V` | V5_MAX=5.101 [1.ª corrida, re-avaliada — BOM inalterada na rev. 2.4] | V5_MAX = 5.101 | cumpre |
| U201 SPX3819 | SPX3819 p.3 VIH >= 2,0 V ; I_EN máx 20 µA | `V_EN = VIN − I_EN·R203 >= 2,0 V` | V5_MIN=4.847, I_EN=2e-05, R203=1e+05 [1.ª corrida, re-avaliada — BOM inalterada na rev. 2.4] | V5_MIN - I_EN*R203 = 2.847 | cumpre |
| U201 SPX3819 | SPX3819 p.2 Dropout (• sobre temp.) 250 mV @ 50 mA | `VIN − VOUT >= 0,25 V` | V5_MIN=4.847, V33_MAX=3.366 [1.ª corrida, re-avaliada — BOM inalterada na rev. 2.4] | V5_MIN - V33_MAX = 1.481 | cumpre |
| U201 SPX3819 | SPX3819 p.7 «requires an output capacitor»; especificações com CL = 1 µF | `COUT >= 1 µF (valor)` | C204=2.2e-06 [1.ª corrida, re-avaliada — BOM inalterada na rev. 2.4] sem MPN de C204 | C204 = 2.2e-06 | cumpre |
| U201 SPX3819 | SPX3819 p.7 «2,2 µF aluminium… 1 µF tantalum… bench testing is the best method» | `estabilidade com condensador CERÂMICO de baixa ESR — especificada?` | ESR_min_especificada=? [1.ª corrida, re-avaliada — BOM inalterada na rev. 2.4] não está neste PDF (rev 2.0.5). [INHERITED] a V4.1 usa o mesmo LDO (U11) com cerâmicos — evidência de campo, não especificação | missing: ESR_min_especificada | **falta dado** |
| U201 SPX3819 | SPX3819 p.3 / p.7 | `BYP = 10 nF` | C208=1e-08 [1.ª corrida, re-avaliada — BOM inalterada na rev. 2.4] | C208 = 1e-08 | cumpre |
| U201 SPX3819 | SPX3819 nota 1 p.2: PD(max) = (TJ(max)−TA)/θJA, θJA(SOT23-5) 191 °C/W | `PD = (VIN−VOUT)·IL + VIN·IGND <= (125−70)/191` | V5_MAX=5.101, VOUT=3.300, IL=0.00672, IGND=0.00025, thJA=191.000, TA=70.000 [1.ª corrida, re-avaliada — BOM inalterada na rev. 2.4] | (V5_MAX-VOUT)*IL + V5_MAX*IGND = 0.01338 ; (125-TA)/thJA = 0.288 | cumpre |
| U201 SPX3819 | SPX3819 p.2 tolerância ±2 % (•) | `banda 3V3_REF = 3,3 V ±2 % → 3,234..3,366 V (usada nas linhas seguintes)` | V33_MIN=3.234, V33_MAX=3.366 [1.ª corrida, re-avaliada — BOM inalterada na rev. 2.4] + regulação de linha 0,2 %/V·(5,08−4,3)=0,16 % e de carga 0,4 % não somadas | V33_MIN = 3.234 ; V33_MAX = 3.366 | cumpre |
| U202 ADR4525 | ADR45xx Rev.G Tabela 2, p.4: «VIN = 3 V to 15 V»; VDO <= 500 mV | `3V3_REF_min >= VOUT + VDO = 2,5 + 0,5 = 3,0 V` | V33_MIN=3.234, VOUT=2.500, VDO=0.5 [1.ª corrida, re-avaliada — BOM inalterada na rev. 2.4] margem 0,234 V; ligação directa (sem ferrite) | V33_MIN - (VOUT+VDO) = 0.234 | cumpre |
| U202 ADR4525 | ADR45xx Rev.G Tabela 11 p.35: COUT mín 1,0 µF ; Tabela 2 p.5: load capacitance 1..100 µF | `C207 + C500 com tolerância −10 % >= 1,0 µF` | C207=1e-06, C500=1e-07, tol=0.1 [1.ª corrida, re-avaliada — BOM inalterada na rev. 2.4] 1,0 µF nominal É o mínimo: qualquer tolerância fica abaixo, antes de polarização DC e temperatura; sem MPN de C207 | (C207+C500)*(1-tol) = 9.9e-07 | **FALHA** |
| U202 ADR4525 | ADR45xx Rev.G p.35 Input Capacitors | `CIN 1..10 µF + 0,1 µF cerâmico em paralelo` | C_in_bulk=2.2e-06, C_in_hf=1e-07 [1.ª corrida, re-avaliada — BOM inalterada na rev. 2.4] C204 + C205/C206 na rede 3V3_REF; a colocação junto ao pino 2 é da F3 | C_in_bulk = 2.2e-06 | cumpre |
| U202 ADR4525 | ADR45xx Rev.G Tabela 2 p.4: IL sourcing <= 10 mA | `I_VREF(MCP3208 máx 150 µA) + I_NTC(70 °C) <= 10 mA` | I_VREF=0.00015, R_NTC_70=2210, R701=5620, VREF=2.500 [1.ª corrida, re-avaliada — BOM inalterada na rev. 2.4] | I_VREF + VREF/(R_NTC_70+R701) = 0.0004693 | cumpre |
| U202 ADR4525 | ADR45xx Rev.G Tabela 2 p.4: load regulation 80 ppm/mA (máx) — interacção com o divisor NTC | `ΔI_NTC(0→70 °C)·80 ppm/mA <= 1 LSB (244 ppm)` | VREF=2.500, R_NTC_0=2.87e+04, R_NTC_70=2210, R701=5620, LR=80.000 [1.ª corrida, re-avaliada — BOM inalterada na rev. 2.4] ppm; erro comum a todos os canais | (VREF/(R_NTC_70+R701) - VREF/(R_NTC_0+R701))*1e3*LR = 19.715 | cumpre |
| U202 ADR4525 | ADR45xx Rev.G p.35 Power Dissipation: PD = (TJ−TA)/θJA ; Tabela 8 p.10 θJA 120 °C/W (2 camadas) | `PD = (VIN−VOUT)·IL + VIN·IQ <= (125−70)/120` | V33_MAX=3.366, VOUT=2.500, IL=0.00047, IQ=0.00095, thJA=120.000, TA=70.000 [1.ª corrida, re-avaliada — BOM inalterada na rev. 2.4] | (V33_MAX-VOUT)*IL + V33_MAX*IQ = 0.003605 | cumpre |
| U202 ADR4525 | ADR45xx Rev.G Tabela 7 p.10 Abs. max supply 16 V | `3V3_REF grampeado <= 16 V` | V_CLAMP_MAX=3.716 [1.ª corrida, re-avaliada — BOM inalterada na rev. 2.4] | V_CLAMP_MAX = 3.716 | cumpre |
| U202 ADR4525 | ADR45xx Rev.G Tabela 2 p.4: TCVOUT B grade 4 ppm/°C (bowtie) | `deriva 25→70 °C = 4·45 ppm <= orçamento RE2 (2000 ppm)` | TC=4.000, dT=45.000 [1.ª corrida, re-avaliada — BOM inalterada na rev. 2.4] ppm | TC*dT = 180.000 | cumpre |
| U202 ADR4525 | ADR45xx Rev.G Tabela 2 p.4: histerese térmica 25→70→0→25 °C: −8 ppm (típ.) | `∣hist∣ <= 1 LSB (244 ppm)` | hist=8.000 [1.ª corrida, re-avaliada — BOM inalterada na rev. 2.4] ppm, típico — não é limite | hist = 8.000 | cumpre |
| U203 TL431B | SLVS543S §9.2.2.2.1 p.26: Vo = (1+R1/R2)·Vref ± Iref·R1  [R1=R204, R2=R205] | `Vo nominal <= 3,7 V (RA4)` | VREF=2.495, R204=4420, R205=1e+04, IREF=4e-06 [1.ª corrida, re-avaliada — BOM inalterada na rev. 2.4] | (1+R204/R205)*VREF + IREF*R204 = 3.615 | cumpre |
| U203 TL431B | SLVS543S §6.13 p.14 (TL431BQ): Vref 2,483–2,507; VI(dev) 34 mV; Iref 4 µA; ∣Z_KA∣ 0,5 Ω  + R ±1 % | `Vo máx = (1+R1·1,01/(R2·0,99))·(Vref_max+VI(dev)) + Iref·R1 + ZKA·I_K <= 3,7 V (RA4)` | VREF_MAX=2.507, VIDEV=0.034, R204=4420, R205=1e+04, IREF=4e-06, ZKA=0.5, I_K=0.04599 [1.ª corrida, ACTUALIZADA para a rev. 2.4] I_K da falha dupla com R601 = 0 Ω (30 V directos no burden): 6 x 7.66 mA; tolerância 1 % ASSUMIDA (R204/R205 sem MPN); com 0,1 % e este I_K dá 3,72 V — continua a falhar | (1+R204*1.01/(R205*0.99))*(VREF_MAX+VIDEV) + IREF*R204*1.01 + ZKA*I_K = 3.728 | **FALHA** |
| U203 TL431B | SLVS543S §6.13 p.14 — mínimo do grampo vs máximo de 3V3_REF | `Vo mín = (1+R1·0,99/(R2·1,01))·(Vref_min−VI(dev)) > 3V3_REF_max (TL431 desligado em operação normal)` | VREF_MIN=2.483, VIDEV=0.034, R204=4420, R205=1e+04, V33_MAX=3.366 [1.ª corrida, re-avaliada — BOM inalterada na rev. 2.4] | (1+R204*0.99/(R205*1.01))*(VREF_MIN-VIDEV) = 3.510 ; V33_MAX = 3.366 | cumpre |
| U203 TL431B | SLVS543S §6.4 p.5: IKA 1..100 mA ; §6.13 Imin 0,7 mA | `corrente de grampo por canal (protector em curto = falha dupla, 30 V no burden com R601 = 0 Ω) e total de 6 canais dentro de 1..100 mA` | I_CH=0.00766, I_TOT=0.04599 [1.ª corrida, ACTUALIZADA para a rev. 2.4] na falha SIMPLES (protector a regular a 40 mA) o clamp total é 0,4–0,9 mA, abaixo do I_min de 0,7 mA: o TL431 nem entra; só a falha dupla o solicita | I_CH = 0.00766 ; I_TOT = 0.04599 | cumpre |
| U203 TL431B | SLVS543S §6.13 p.14: Ioff <= 0,5 µA (VKA = 36 V) | `consumo do grampo desligado em operação normal desprezável (<1 % de IQ do ADR4525)` | IOFF=5e-07, IQ_ADR=0.0007 [1.ª corrida, re-avaliada — BOM inalterada na rev. 2.4] | IOFF = 5e-07 | cumpre |
| U203 TL431B | SLVS543S §9.4 p.31 «be sure that the capacitance is within the stability criteria shown in Figure 6-16 and 6-18»; Fig.6-18 p.18 | `C_L no cátodo fora da zona de oscilação: C_L <= 0,01 µF ou C_L >= 6 µF (curva A, VKA=Vref; a 3,6 µF a curva A está em ≈25 mA)` | C_L=3.6e-06 [1.ª corrida, re-avaliada — BOM inalterada na rev. 2.4] C204+C205+C206+C403+C501+C502 (ferrites transparentes a <1 MHz). VKA = 3,6 V fica entre a curva A (Vref) e a B (5 V, estável acima de ~1,5 µF): não demonstrável estável a 3–21 mA; só a bancada ou C_L ≥ 10 µF fecham | C_L = 3.6e-06 | **FALHA** |
| U203 TL431B | SLVS543S §6.3 p.5 RθJA(DBZ) 206 °C/W ; §6.4 nota(1) PD = (TJ−TA)/θJA | `PD = Vo·I_K(6 canais) <= (125−70)/206` | Vo=3.716, I_K=0.04599, thJA=206.000, TA=70.000 [1.ª corrida, ACTUALIZADA para a rev. 2.4] | Vo*I_K = 0.1709 ; (125-TA)/thJA = 0.267 | cumpre |
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
